Lin-Guanguo/hardware-lab/projects/nfc-business-card/hardware/routing-space-study.md

# 布线空间先行研究

## 当前确定方案

更新于 **2026-09-21**。在重新生成 FreeCAD 外壳或修改 EDA 主工程前，先验证一项平面分区：屏幕固定在左上，长条电池放左下，NFC 保留在右上，USB、充电、电源、屏幕升压和主控尝试集中到右下。这个文件只记录空间假设，不冻结电池型号，也不替换 E9。

研究输入为 84 × 52 mm 外形、现有屏幕/FPC/NFC 参考框和 E9 的功能块。脚本会生成候选电池的二维包络与右下自由区，输出到被忽略的 `artifacts/studies/routing-space/`；它不打开 FreeCAD，不修改 `.FCStd`，也不修改 EasyEDA 工程。

## 先得到的结论

- 屏幕下边约在 `y = 18.5 mm`，假设板内边距为 1.5 mm 后，右下布线区的可用高度约 **16.5 mm**。这是当前分区的主要高度约束。
- 301030 / 301230 横放在左下、从 `x = 2 mm` 开始时，右下连续自由区约 **48.5 × 16.5 mm**；301423 和 301525 较短，右下宽度约 **54.5 / 53.5 mm**。
- 该自由区大于本轮先采用的 **22 × 15 mm USB/电源规划包络**，也大于包含主控和按键的 **40 × 16.5 mm 初步包络**。这些包络是早期筛选值，不是 DRC 或板厂保证。
- 电池放左下会与当前左下的 U1/BLE 天线保留区重叠；因此下一轮必须把 U1 作为右下功能块的一部分重新摆放，并先检查模块天线朝向和边缘净空。
- 这个分区不会侵入当前屏幕、FPC 路径或右上 NFC 参考框，机制上比“电池占掉 NFC 区”更稳妥。

因此，问题已经从“整块板没有通道”缩小为两个可验证问题：

1. 右下 16.5 mm 高的长条能否同时容纳 USB-C 局部扇出、U5/U6、充电器、电源外围和主控；
2. U1 移到右下后，BLE 天线净空是否仍可沿板边保留。

如果这两个问题通过，才值得继续生成新的 CAD 外壳；如果 U1 天线无法在右下安置，应退回 301423/301525 这类较短电池，或保留 U1 左下并重新计算右下最小宽度。

## 候选电池的平面比较

截图中的尺寸和容量是卖家标称。型号中的几何数字可作为初筛，不能代替带保护板、胶带、焊点和引线的最大包络。尤其是 301030，不同供应商目录可出现 60–70 mAh，不能仅凭型号接受 100 mAh；301230 的公开商品示例为 3 × 12 × 30 mm、110 mAh、带 PCM，但也不能证明淘宝同店同批次一致。

| 型号 | 本研究使用的标称包络 | 右下自由区（电池从 x=2 mm 开始，留 2 mm 间隙） | 初步判断 |
| --- | --- | ---: | --- |
| 301030 | 30 × 10 × 3 mm | 48.5 × 16.5 mm | 最窄；容量和完整包体需重点核对 |
| 301230 | 30 × 12 × 3 mm | 48.5 × 16.5 mm | 容量/宽度较平衡，优先询样 |
| 301423 | 24 × 14 × 3 mm | 54.5 × 16.5 mm | 更短，右下更宽；电池左下高度占用较多 |
| 301525 | 25 × 15 × 3 mm | 53.5 × 16.5 mm | 宽且标称容量较低，暂不优先 |

## 下一轮的边界

下一轮只在 EDA 副本中做右下功能块布局，不先改 FreeCAD：

- 保留 E9 原文件；新副本只移动 U1、J1、U5/U6、CC/串联电阻、U2/U3 及其去耦、按键和 SWD；
- 屏幕、J2/FPC 路径、NFC 参考框先不动；
- 先用真实封装检查右下 `16.5 mm` 高度和 USB 插座板边开口；
- 只试 USB_DP/DM、CC1/CC2、VBUS 与 U1 入口，不自动铺开普通信号；
- 通过条件是：关键出口有连续通道、没有新增器件/板边碰撞、U1 天线净空有明确边界；
- 只有通过后，才把验证后的坐标同步到新的 FreeCAD 外壳模型。

可重复命令：

```sh
python3 projects/nfc-business-card/scripts/routing-space-study.py \
  --output-dir projects/nfc-business-card/artifacts/studies/routing-space/<new-run>
```

输出中的 `routing-space-study.json` 是数值记录，`routing-space-study.svg` 是平面比较图。输出目录属于临时验证产物，不提交 Git；脚本和本说明保留。
