Lin-Guanguo/hardware-lab/projects/nfc-business-card/hardware/pcb-e10-button-right.md

# E10 按键右移对照

E10 从 E9 独立复制，将 SW1/SW2/SW3 从 `44.5 mm` 整体移到 `50.0 mm`，板框、USB-C 和其他器件不变。保存重开后几何检查通过，仍为 56 个元件、242 个焊盘、0 段铜线、0 个过孔，DRC 224 条。

右移没有减少 USB/CC 的现有瓶颈；三个按键网络连接到左侧 U1，最短出线距离增加约 5.5 mm。因此 E10 只作为比较工程保留，当前采用 E9 的按键位置。若后续 USB 数据或 VBUS 的明确走线结果显示右侧需要连续通道，再把按键位置与外壳开孔一起复评。
