Lin-Guanguo/hardware-lab/projects/image-oracle/docs/prototype-milestone.md

# 拼接原型阶段收尾与后续路线

日期：2026-09-19。用户确认第三个程序“都正常，效果符合预期”，本阶段定义为：**相机、屏幕与按键的桌面拼接原型完成**。

## 已完成的工作

| 内容 | 当前结果与入口 |
| --- | --- |
| 到货和板卡核对 | 已整理[器件清单](../../../docs/inventory.md)，区分清单、照片与实测结论 |
| 连接、备份与恢复 | USB-UART、原生 USB、下载模式与正常启动流程已记录；保留完整 16 MiB 原厂备份，见[相机启动记录](camera-bringup.md) |
| 程序一：单帧拍照 | [camera_serial](../firmware/camera_serial/README.md)，OV3660 320×240 JPEG 经 USB 保存到 Mac |
| 程序二：显示与按钮 | [display_serial](../firmware/display_serial/README.md)，ST7789 显示、MID 计数；修复快速连按漏计数和 USB 日志阻塞 |
| 程序三：整合原型 | [oracle_live](../firmware/oracle_live/README.md)，左侧约 20 FPS 预览、MID 定格到右侧、下方显示 TRUE/FALSE；用户确认交互、方向和颜色正常 |
| 算法与实机验证 | 固定像素结果可复现；真实右图导出后重算哈希及答案一致；无 USB 读取端时预览和采样继续运行，见[整合实测](oracle-bringup.md) |
| 接线与知识沉淀 | 四张带主板外形、完整丝印和数字序号的 [HTML 接线图](../wiring-diagrams/README.md)；[响应性经验](responsive-input-display.md)、[USB 知识](usb-uart-notes.md)及[统一画图方法](../../../docs/wiring-diagrams.md) |

当前板上程序是 `oracle_live`，旧程序是可单独构建、烧录的实验基线。三个工程固定 Arduino CLI 1.5.1 与 ESP32 core 3.3.11；屏幕相关依赖版本和实际命令保存在对应工程 README。普通断电重插会启动当前已烧录程序，不会自动切换工程。

## 当前边界

- 结构仍是开发板、现成模块、面包板共地和杜邦线连接，桌面体积大、线材分散；尚无定制 PCB、焊接成品或外壳。
- 五向按键目前只接 COM 与 MID，其他方向、SET、RST 未接入；其余传感器、音频等模块未通电验收。
- 答案是冻结缩略图的确定性哈希映射；照片仅在 RAM，断电丢失。尚未扩展答案库或持久保存。
- 已有短时间实机回归和用户体验验收；长时间连续运行、专项长按测试、更高分辨率及整机功耗测量未完成。
- 本阶段完成的是交互功能原型；尺寸、固定方式、连接可靠性和成品装配将进入下一阶段处理。

## 路线一：拼接更多传感器，继续实验

目标是利用现有器件探索更多输入和互动。候选来自已购清单：SHT30 温湿度、GY-302 光照、触摸模块、旋转编码器，以及五向按键的其余功能；具体型号、工作电压和可用 GPIO 在每次实验前核对。

每次选一个模块，先完成独立读取或事件测试，再决定是否接入屏幕页面；保留当前原型作为回退基线。每个实验记录接线、驱动依赖、实际命令、读数和验证结论，接线图沿用现有格式。不要因为增加传感器，就默认改变“图像是 Oracle 唯一变化输入”的规则；若要混入环境数据，应另行明确算法版本。

完成一个实验的标准是能稳定读取或响应、交互仍及时、有可复现记录。后续再决定哪些功能值得保留到紧凑版本，不预先把全部模块纳入最终装置。

## 路线二：焊接、定制电路板与 3D 打印，做紧凑装置

目标是把已经能工作的交互收进可拿起、可固定、可维护的小装置，减少桌面杜邦线。

推进顺序先作为工作草案记录，具体结构和工艺待启动此路线时验证：

1. **确定保留的功能与布局。** 测量当前开发板、屏幕、摄像头、按键和接口的实际外形、孔位及高度；决定显示方向、镜头位置、按键位置、USB 插拔与复位操作空间。
2. **整理连接与装配方式。** 明确哪些模块可插拔、哪些连接焊接固定；比较短线束、洞洞板／转接板和承载现有模块的 PCB。更换接法前整理原理连接表和引脚占用。
3. **定制 PCB。** 在功能和布局相对稳定后绘制原理图与 PCB，逐项核对电源、接口和模块尺寸，再进行打样、焊接和通电验证。是否进一步用模组或芯片替代现成开发板，留待体积需求明确后决定。
4. **3D 打印外壳。** 先验证安装框架、开孔和固定点，再结合实际板卡／线束调整外壳；记录模型、版本和试装问题。开始有真实设计内容时才创建 `enclosure/`。
5. **整机复测。** 验证装配后取景、显示、按键、USB 编程、稳定供电和持续运行，并确认连接固定与拆装维修是否可行。

两条路线可以交替进行；传感器实验保留扩展空间，紧凑版本在绘板前确认本次要保留的功能。本次只记录方向，没有选定制造服务、材料、预算或最终尺寸，也没有发起采购或制作。

## 可恢复基线与归档

当前第三个程序的烧录文件与对应源码已另存本地：

```text
projects/image-oracle/artifacts/firmware/oracle-live-20260919/
```

目录内含四段烧录二进制、`flash_args`、保持相对路径的主程序与头文件，以及 `SHA256SUMS`。8 个文件复制后比对一致，以下校验通过：

```sh
(
  cd projects/image-oracle/artifacts/firmware/oracle-live-20260919
  shasum -a 256 --check SHA256SUMS
)
```

恢复时使用[第三个程序说明](../firmware/oracle_live/README.md#构建烧录与恢复)中的烧录流程，将工作目录换成该备份目录；先确认目标设备和端口。需要从源码重新构建时，使用仓库中的工程及固定工具链。

Git 提交包含源码、脚本、测试、接线图、器件清单、资料来源和实验记录；原始下载、工具链、构建缓存、照片、串口日志、原厂备份及上述二进制基线保存在本机忽略目录。重新克隆仓库不会带回这些本地文件。

## 收尾检查

- Mac 上重新编译运行 `button_debouncer_test.cpp` 与 `oracle_image_test.cpp`，消抖和图像算法测试通过；命令分别见[显示工程](../firmware/display_serial/README.md#编译)与[Oracle 工程](../firmware/oracle_live/README.md#固定算法)。
- 仓库 shell、Python、JSON 语法和 Markdown 本地链接检查通过；8 份接线图 HTML 的内联脚本经 `node --check` 解析通过。语法检查不代替此前的实际显示验证。
- `git diff --cached --check` 通过，提交清单已核对；固件二进制、照片、日志、下载与构建目录的忽略规则生效。
- 本次收尾只更新文档和归档，不重新烧录；实机结果沿用本阶段已完成的测试与用户验收。
