Lin-Guanguo/hardware-lab/projects/nfc-business-card/archive/README.md

# NFC design history

## 当前确定方案

The [active R1 index](../README.md) is the entry point for current work. This archive preserves superseded material; its old "current" statements and manufacturing gates describe their original dates.

- [pre-r1/hardware](pre-r1/hardware/): E-series design studies and evidence.
- [pre-r1/enclosure](pre-r1/enclosure/): superseded models and renders.
- [pre-r1/scripts](pre-r1/scripts/): historical automation; restore the corresponding Git state to reproduce old workflows, rather than running these against R1.
- [pre-r1/docs](pre-r1/docs/): early and alternate plans.
- [pre-r1/readmes](pre-r1/readmes/): previous indexes and progress notes.
- [Move manifest](pre-r1/move-manifest.json): original and new paths, with hashes before relocation. Historical JSON evidence retains its original embedded paths.
- [Historical native EDA projects](../../../eda/archive/nfc-business-card/): E6–E20 and intermediate database checkpoints.

No historical design files were discarded. Markdown links were rebased where targets could be resolved. Local generated outputs remain in `artifacts/archive/` and are not committed.

[Pre-optimization R1 checkpoint](r1-checkpoint/) preserves the original rectangular coil snapshot, Gerber comparison and mechanical source; complete state is commit `ccf9f92`.
