Lin-Guanguo/hardware-lab/projects/nfc-business-card/archive/pre-r1/readmes/projects/nfc-business-card/scripts/README.md

# 电子名片脚本

## 当前确定方案

**R1 workflow:** [check-r1-copper.py](../../../../../../scripts/check-r1-copper.py) checks complete copper including pours, [check-r1-nfc.py](../../../../../../scripts/check-r1-nfc.py) proves the winding is not bypassed, [check-r1-delivery.py](../../../../../../scripts/check-r1-delivery.py) compares the frozen manufacturing package, and [check-r1-case.py](../../../../../../scripts/check-r1-case.py) reopens CAD and checks debug holes and closed meshes. [Commands and evidence](../../../../../../hardware/pcb-r1-delivery.md). Export the guarded live snapshot with [eda-export-r1-snapshot.js](../../../../../../scripts/eda-export-r1-snapshot.js); render actual copper with [render-r1-copper.py](../../../../../../scripts/render-r1-copper.py).

## E20D placement tools

**Current E20D workflow:** [check-e20d-layout.py](../../../../scripts/check-e20d-layout.py) checks placement, USB translation and rear NFC copper exclusions. [e20-clear-shell.py](../../../../../../enclosure/e20-clear-shell.py) takes `NFC_E20_CONFIG=.../e20d-design.json` to generate the coordinated 5.8 mm enclosure. [check-e20b-body-fit.py](../../../../scripts/check-e20b-body-fit.py) accepts `NFC_BODY_REVIEW_REV=e20d` and `NFC_E20_OUT` for native body checks; [render-e20d-front-rear.py](../../../../scripts/render-e20d-front-rear.py) draws native placement plus the explicitly illustrative coil reservation. [Commands, evidence and remaining gates](../../../../hardware/pcb-e20d-front-rear.md).

## Historical E14–E19 workflow

**J1 间隙检查已纠正：**`check-e16-board-fit.py` 现在将统一参考平面的高度差单独标为 `height_below_reference_ceiling_mm`，并用完整 J1 与壳体的 `distToShape` 报告真实距离。E19 对 V7 的名义值为上壳约 **0.34 mm**、下壳约 **0.40 mm**；下文旧的 0.13 mm 仅为参考平面高度差。

更新于 **2026-09-23**。E16 板（三键、L 形板框、右边缘 USB 缺口）的电气连通已核：PCB 原生 DRC 连接 0、只剩 24 项 `Board Outline to SMD Pad`（同一处 0.2007 mm 焊盘到板边的两种分类）、逐引脚网表 56 位号 / 234 引脚 / 0 差异。**增强后的制造包检查发现 Gerber 板框多路径和冲突机械层，E16/E18/E19 当前导出均不通过，不能下单。**外壳 V7 对真实元件模型为名义 0 干涉，尺寸公差仍需核验。当前 CAD 入口是 [e16-enclosure-right-mid-usb-v7.py](../../../../enclosure/e16-enclosure-right-mid-usb-v7.py)，配套校验脚本 [check-e16-board-fit.py](../../../../scripts/check-e16-board-fit.py) 与 [check-e16-usb-plug.py](../../../../scripts/check-e16-usb-plug.py)。E14 空间研究（[e14-layout-study.py](../../../../enclosure/e14-layout-study.py)、[e14-enclosure-v1.py](../../../../enclosure/e14-enclosure-v1.py)）与 V1–V6 外壳样件保留作历史入口。

新的 PCB 开工入口是 [E15 清理版 PCB 开工记录](../../../../hardware/pcb-e15-clean-layout.md)。E15 图页位于 E14 `.eprj2` 工程内；其审查快照由 [generate-e15-clean-layout-svg.py](../../../../scripts/generate-e15-clean-layout-svg.py) 从保存后的 E15 数据生成。该脚本只渲染审查图，不修改 EasyEDA 工程。

右侧中部 USB 方向由 [E16 布局方案](../../../../hardware/pcb-e16-usb-right-mid.md) 推进：[plan-e16-right-mid.py](../../../../scripts/plan-e16-right-mid.py) 用 E15 快照的真实焊盘坐标比较"原布局 / 新方案"的焊盘、模块外形、NFC 保留区和天线净空，输出 [e16-right-mid-plan.json](../../../../hardware/e16-right-mid-plan.json)；[generate-e16-right-mid-svg.py](../../../../scripts/generate-e16-right-mid-svg.py) 直接读取 [e16-right-mid-snapshot.json](../../../../hardware/e16-right-mid-snapshot.json) 画当前审查图——L 形板框、双面铜箔、焊盘与过孔实形、56 个位号、板面自带的层 13 说明文字、禁布区与显示包络，外加右侧的方案面板。禁布区矩形用的是文档记录的边界，因为层 12 的多边形不经桥接导出；其余几何都取自快照。快照用 [eda-export-e16-snapshot.js](../../../../scripts/eda-export-e16-snapshot.js) 从 E16 图页重新导出，否则图会停在旧状态：

```sh
node projects/nfc-business-card/scripts/eda-exec-wait.mjs \
  projects/nfc-business-card/scripts/eda-export-e16-snapshot.js 60000 > /tmp/snap.json
python3 -c "import json,pathlib;d=json.load(open('/tmp/snap.json'))['result'];p=pathlib.Path('projects/nfc-business-card/hardware/e16-right-mid-snapshot.json');p.write_text(json.dumps(d,indent=1,ensure_ascii=False)+chr(10))"
python3 projects/nfc-business-card/scripts/generate-e16-right-mid-svg.py
```

铜箔连通性单独核查：[check-e16-copper-connectivity.py](../../../../scripts/check-e16-copper-connectivity.py) 按真实铜箔宽度判断"两块铜是否搭上"，检查每个网络的焊盘/过孔是否在同一铜簇、以及有没有悬空铜端。**E16 的原生 DRC 即使断网也报"连接 0"，所以动铜箔后必须跑这个脚本**（当前：48 个网络全部连通、死铜端 0）：

```sh
python3 projects/nfc-business-card/scripts/check-e16-copper-connectivity.py
```

原理图与 PCB 的一致性用逐引脚比对核实：[eda-export-pcb-pins.js](../../../../../../scripts/eda-export-pcb-pins.js) 导出 PCB 焊盘网络，[check-netlist-consistency.py](../../../../../../scripts/check-netlist-consistency.py) 与原理图导出的 netlist 做双向差集（当前 56 位号 / 234 引脚 / 0 处差异）：

```sh
node projects/nfc-business-card/scripts/eda-exec-wait.mjs \
  projects/nfc-business-card/scripts/eda-export-pcb-pins.js 60000 > /tmp/pcb-pins.json
# 原理图那份 netlist 已随仓库保存（与验证过的那份 sha256 一致），无需再从客户端导出
python3 projects/nfc-business-card/scripts/check-netlist-consistency.py \
  --sch projects/nfc-business-card/hardware/records/e16-sch-netlist.enet \
  --pcb /tmp/pcb-pins.json
```

**动铜箔之前先离线校验**：原生 DRC 只有铜箔落盘后才能看到结果，而 E16 的"连接 0"并不能证明连通。[plan-nfc-coil.py](../../../../scripts/plan-nfc-coil.py) 按记录好的几何生成 E16 线圈方案（6 圈矩形螺旋 + 两端馈线 + 顶层跨接 + 2 个过孔），[check-proposed-route.py](../../../../../../scripts/check-proposed-route.py) 拿这份方案与实时快照逐点比：线-线 0.102、焊盘/过孔-线 0.152、铜到板边 0.300、孔到孔 0.300，外加"线路自身间距"和禁布区规则（两份禁布区只禁填充/铺铜，允许走线）：

```sh
python3 projects/nfc-business-card/scripts/plan-nfc-coil.py --write     # -> hardware/e16-nfc-coil-plan.json
python3 projects/nfc-business-card/scripts/check-proposed-route.py \
  --route projects/nfc-business-card/hardware/e16-nfc-coil-plan.json
# 期望：ok=true，且 within_route 最差约 0.150 mm（环间距）、其余间隙都在 2 mm 以上
```

方案文件里同时写着落盘前的两个前提：把保留区规则从 `[2,6,5,7]` 放宽为 `[2,6,7]`（去掉禁止走线），以及选择线圈的网表表示（合并两个 NFC 网络，或加一个天线器件+定制封装）。

外壳叠层剖视图由 [generate-e16-v5-section-svg.py](../../../../scripts/generate-e16-v5-section-svg.py) 从几何报告生成（三张切片 + 图例，数字随报告更新）；[generate-e16-height-budget-svg.py](../../../../scripts/generate-e16-height-budget-svg.py) 画的是 5 mm 叠层高度账（电池区剖面 + 各层厚度标注，输出 `enclosure/nfc-card-e16-height-budget.svg`）：

```sh
python3 projects/nfc-business-card/scripts/generate-e16-v5-section-svg.py
```

外壳样件的着色等轴测图与正视顶视图由 [render-stl-iso.py](../../../../../../scripts/render-stl-iso.py) 直接从 STL 生成（不需要 FreeCAD GUI），输出到被忽略的 `enclosure/renders/`：

```sh
python3 projects/nfc-business-card/scripts/render-stl-iso.py
```

NFC 线圈估算：`estimate-nfc-coil.py` 按改良 Wheeler 公式给出螺旋电感、直流电阻、13.56 MHz 谐振电容与 Q，用来判断某块面积能不能做到 1–2 µH：

```sh
# 外圈尺寸按实测可用区填（E16 现在是 10.4 x 21.3 mm，不是早先估的 17 x 21）
python3 projects/nfc-business-card/scripts/estimate-nfc-coil.py --outer 10.7,21.5 --turns 4 5 6 7 8 --width 0.25
```

E16 最初按经验留 5 mm 金属净空，得出 **x 60.60–71.00、y 27.60–48.90** 的六圈候选；这不是硬性射频限制。后续 E18/E19 对比发现其面积使用偏保守，E19 已在独立图页放大为五圈、20.2 × 21.3 mm；实物射频仍待测，详见[面积复核](../../../../hardware/nfc-coil-area-process-review.md)。

空铜区查询：`report-free-space.py` 把快照按 0.1 mm 网格栅格化，给指定区域/层打印占用图并列出最大空矩形（带设计规则余量）。放电池引线走廊、NFC 落点、临时测试点之前先用它量一遍，别凭眼看：

```sh
python3 projects/nfc-business-card/scripts/report-free-space.py --region 33,0,46,19 --layer 1 --limit 3
python3 projects/nfc-business-card/scripts/report-free-space.py --region 54,2,72,26 --layer 2 --limit 3
```

制造包核对：`eda-export-e16-manufacture.js` 一次导出 Gerber/BOM/CPL/装配 PDF（文件落在 `~/Downloads/.cn.lceda.pro.*` 随机名），[collect-e16-manufacture.py](../../../../scripts/collect-e16-manufacture.py) 按内容识别这四个文件并拷成 `artifacts/manufacture/` 下的规范名，`check-e16-manufacture.py` 再把结果与当前快照逐点比对（**唯一闭合板框路径、无冲突机械层轮廓**、板框顶点、钻孔孔数、位号集合、贴装坐标偏差）并写 `manifest.json`。**当前 E16/E18/E19 的重导包均返回 `ok=false`，须修复板框源图或导出配置后重导。**

```sh
node projects/nfc-business-card/scripts/eda-exec-wait.mjs projects/nfc-business-card/scripts/eda-export-e16-manufacture.js 120000
python3 projects/nfc-business-card/scripts/collect-e16-manufacture.py    # 从 ~/Downloads 归纳到 artifacts/manufacture/
python3 projects/nfc-business-card/scripts/check-e16-manufacture.py
```

E19 板框清理仅用于审查：`prepare-outline-review-package.py --source projects/nfc-business-card/artifacts/coil-api-study/expanded-manufacture --output projects/nfc-business-card/artifacts/coil-api-study/outline-cleaned-review`。脚本只接受已复核的 Gerber 结构，删去 J1 辅助线和旧机械参考矩形；输出须再以 E19 快照运行上述检查器。**EDA 源图和正式导出流程仍待修复，审查包不是下单放行文件。**

打印件（STL）的网格体检：[check-e16-print-meshes.py](../../../../scripts/check-e16-print-meshes.py) 直接打开三个 V7 STL，报告是否封闭实体、自相交、非流形边、退化面/重复点，并核对 84 × 52 外框与 4.5 mm 顶面。几何报告查的是 FreeCAD 实体，切片软件只看 STL，所以两个检查都要跑：

```sh
/Applications/FreeCAD.app/Contents/Resources/bin/freecadcmd \
  projects/nfc-business-card/scripts/check-e16-print-meshes.py
```

外壳与**真实元件模型**的干涉检查（不只简化参考盒）：先用 [eda-export-e16-3d.js](../../../../scripts/eda-export-e16-3d.js) 从 E16 图页导出带元件模型的 STEP，等 `~/Downloads/.cn.lceda.pro.*` 的字节数稳定后复制到 `/tmp/e16-board.step`，再用 [check-e16-board-fit.py](../../../../scripts/check-e16-board-fit.py) 在 FreeCAD 里把板抬到 z=0.7 与 V7 上下壳求交：

```sh
node projects/nfc-business-card/scripts/eda-exec-wait.mjs projects/nfc-business-card/scripts/eda-export-e16-3d.js 120000
cp ~/Downloads/.cn.lceda.pro.XXXXXX /tmp/e16-board.step
/Applications/FreeCAD.app/Contents/Resources/bin/freecadcmd projects/nfc-business-card/scripts/check-e16-board-fit.py
```

脚本会过滤导出文件里堆在原点、没有放置的库模型，输出壳体干涉、三条加强筋带（z 3.6–4.0）干涉、三个键帽与实物元件的干涉，以及最高元件到上盖内表面的余量；有真实干涉时退出码为 1。默认读 V7 模型，可用 `--enclosure=...` 换版本。当前结果：918 个导出实体、474 个在板上，壳体/加强筋/三个键帽 **0 干涉**，最高件 J1 余量 0.13 mm。

[pcb-maze-router.py](../../../../../../scripts/pcb-maze-router.py) 是补线阶段用的离线两层迷宫布线器。输入一份几何快照（`pcb_PrimitiveLine` / `pcb_PrimitiveVia` / `pcb_PrimitivePad` 的坐标，单位 mil）和任务表（`[网络, 起点, [目标...]]`，单位 mm），按实际设计规则做障碍扩张后用矢量桶队列 Dijkstra 求路径，输出线段与过孔清单；`--rip` 可先剔除挡路的既有线段，`--pen` 控制拥塞代价让多条线并行挤同一走廊，`--width` 调整线宽。它只写 JSON，改工程由单独的 EasyEDA 脚本完成：

```sh
python3 projects/nfc-business-card/scripts/pcb-maze-router.py --dump snapshot.json --tasks tasks.json --rip rip.json --width 0.15 --pen 40 --out routes.json
```

注意过孔必须 ≥ 7.9 mil 内径 / 11.9 mil 外径，否则既报物理错误又不会被连通性判定接受；DRC 面板是异步的，触发后等待再读，保存重开才得到真实数字。

E14 实际平面图由 [generate-e14-eda-layout-svg.py](../../../../scripts/generate-e14-eda-layout-svg.py) 从 [e14-eda-snapshot.json](../../../../hardware/e14-eda-snapshot.json) 生成；快照同时保留 [器件/焊盘坐标](../../../../hardware/e14-eda-components-pins.json)，用于核对 EasyEDA 保存重开后的真实板框、机械图元和元件位置。该脚本不会修改 EDA 工程。

外壳坐标协调样件由 [e14-enclosure-v2-eda-coordinate.py](../../../../enclosure/e14-enclosure-v2-eda-coordinate.py) 生成；复核使用 [check-e14-enclosure-v2.py](../../../../scripts/check-e14-enclosure-v2.py)。V2 将 USB 开口放在 E14 实际 J1 所在的 y=0 边，只用于解决 PCB/外壳坐标关系。

按键为**三颗**：SW1 (38.1, 3.30)、SW3 (38.1, 15.10) 一列 + 三角第三点 SW2 (46.3, 8.80)，外壳 V7 开三个键孔；菜单仍按两键（一级/二级切换）定义，第三颗接在原本空置的 `KEY_NEXT_N` 上，功能待定。

E14 模型可直接复现：`/Applications/FreeCAD.app/Contents/Resources/bin/freecadcmd projects/nfc-business-card/enclosure/e14-layout-study.py`；几何检查使用 `freecad-study.py check`，视觉检查使用一次 GUI 预览。统一输出到新目录或新文件，保留已有模型；不覆盖其他窗口中的手工或未保存修改。

E14 生产化门槛记录见 [pcb-e14-manufacturing-gates.json](../../../../hardware/pcb-e14-manufacturing-gates.json)。它只记录当前快照和放行条件，不生成制造文件，也不会把未确认的电池尺寸或空间包络当成供应商规格。

器件与**板子材料**的干涉检查：[check-e16-board-clearance.py](../../../../scripts/check-e16-board-clearance.py) 把同一份 STEP 里每个实体与按当前板框拉出的 0.8 mm 板体求交，抓"器件插进板子里"这类外壳检查看不到的问题：

```sh
/Applications/FreeCAD.app/Contents/Resources/bin/freecadcmd \
  projects/nfc-business-card/scripts/check-e16-board-clearance.py
```

这个脚本在 2026-09-23 抓出了真问题：J1 模型与板子相交约 11 mm³，全部落在 x 76.70–77.50 这段 0.80 mm 条带里，而封装自带的板边线在 76.704——说明缺口内缘画浅了。改到 76.704 后当前**通过**（`real_intrusions: 0`）：报告里仍会列出四颗壳脚焊盘被封装画成穿板方块的碎片和 4 µm 贴面接触，两类都按 `surface_contact` / 面积体积阈值标成非真实。结论与复验见 [E16 记录的下标基准复核](../../../../hardware/pcb-e16-usb-right-mid.md#j1-与板框基准复核2026-09-23已修正并复验)。

插头侧复核：[check-e16-usb-plug.py](../../../../scripts/check-e16-usb-plug.py) 按 GCT mating view 的 8.34 × 2.56 mm 插头截面，在 V7 报告量到的 J1 包络上对中插到底，检查插头与注塑头是否撞壳：

```sh
/Applications/FreeCAD.app/Contents/Resources/bin/freecadcmd \
  projects/nfc-business-card/scripts/check-e16-usb-plug.py
```

当前结果：金属壳对上/下壳 **0 / 0 mm³**；能插到接插面的最大注塑头宽度 **9.20 mm**（缺口 9.24 mm），更宽的注塑头会停在卡边、少插 0.8 mm（接插面在卡边内侧 0.8 mm）。

门槛检查：

```sh
python3 projects/nfc-business-card/scripts/check-e14-gates.py
```

EDA 最新为 [84 × 52 E6 功能块工程](../../../../hardware/pcb-e6-84x52-blocks.md)。新增 [check-e6-netlist.py](../../../../scripts/check-e6-netlist.py)，检查 56 元件、234 项原理图引脚与 234 项 PCB 元件焊盘网络；不验证铜线连通、DRC、功耗或 RF：

```sh
python3 projects/nfc-business-card/scripts/check-e6-netlist.py projects/nfc-business-card/hardware/e6-blocks-circuit.enet --pcb projects/nfc-business-card/hardware/pcb-e6-84x52-blocks.json --pcb-netlist projects/nfc-business-card/hardware/e6-blocks-pcb.enet
```

## 常用命令

从仓库根目录运行；环境为本机 FreeCAD 1.1.3 arm64，默认运行时位于 `/Applications/FreeCAD.app/Contents/Resources`。

```sh
/Applications/FreeCAD.app/Contents/Resources/bin/freecadcmd projects/nfc-business-card/enclosure/e14-layout-study.py
/Applications/FreeCAD.app/Contents/Resources/bin/freecadcmd projects/nfc-business-card/enclosure/e14-enclosure-v1.py
/Applications/FreeCAD.app/Contents/Resources/bin/freecadcmd projects/nfc-business-card/enclosure/e14-enclosure-v2-eda-coordinate.py
python3 projects/nfc-business-card/scripts/freecad-study.py check projects/nfc-business-card/enclosure/pcba-e14-battery-layout.FCStd
python3 projects/nfc-business-card/scripts/freecad-study.py preview projects/nfc-business-card/enclosure/pcba-e14-battery-layout.FCStd
printf '%s\n' 'exec(open("projects/nfc-business-card/scripts/check-e14-enclosure-v2.py").read())' | /Applications/FreeCAD.app/Contents/Resources/bin/freecadcmd --console

python3 projects/nfc-business-card/scripts/freecad-study.py generate --variant e6-84x52-detail
python3 projects/nfc-business-card/scripts/freecad-study.py check projects/nfc-business-card/enclosure/pcba-e6-84x52-detail.FCStd
# Optional: one temporary GUI process, then exit.
python3 projects/nfc-business-card/scripts/freecad-study.py preview projects/nfc-business-card/enclosure/pcba-e6-84x52-detail.FCStd
```

生成命令复现宏中的参数，不会导入已保存模型里的手工修改。[freecad-worker.py](../../../../../../scripts/freecad-worker.py) 是内部工作脚本，不直接用系统 Python 启动。完整环境、输出与限制见[软件说明](../../../../../../docs/software.md#84--52-实际封装细化)。

## 其他检查与历史变体

### 布线空间先行研究

在修改 CAD 或 EasyEDA 之前，可先运行 [routing-space-study.py](../../../../scripts/routing-space-study.py) 比较长条电池和右下布线区。它只生成忽略的 JSON/SVG，不覆盖模型或工程：

```sh
python3 projects/nfc-business-card/scripts/routing-space-study.py \
  --output-dir projects/nfc-business-card/artifacts/studies/routing-space/<new-run>
```

研究结论与限制见[布线空间先行研究](../../../../hardware/routing-space-study.md)。

[check-schematic-netlist.py](../../../../../../scripts/check-schematic-netlist.py)核对原 27 元件草案的关键网络，不验证新增 J2/U4/U5、PCB 布线或可制造性：

```sh
python3 projects/nfc-business-card/scripts/check-schematic-netlist.py projects/nfc-business-card/hardware/schematic-draft.enet
```

`baseline`、`e6-302030`、`e6-bottom-usb`、`e6-84x52` 和 `e6-83x51` 保留用于复现旧比较；日常继续当前方案时选择 `e6-84x52-detail`。

### EDA 元件关联复核

`check-e6-netlist.py` 可追加 `--pcb-netlist <PCB 导出的 .enet>`，核对两侧元件集合、Unique ID、封装和引脚网络。与 `--pcb` 的焊盘网络快照检查互补；需从同一工程的正确原理图/PCB 上下文重新导出，不混用旧会话文件。本轮先检出 27 个关联 ID 差异，修正并保存重开后通过。当前功能块副本的复验输入为 `hardware/e6-blocks-circuit.enet`、`hardware/e6-blocks-pcb.enet` 和 `hardware/pcb-e6-84x52-blocks.json`；原 E6 网表与快照保留作历史比较。
