Lin-Guanguo/hardware-lab/projects/nfc-business-card/archive/pre-r1/docs/design-start.md

# 首版设计启动

日期：2026-09-19。

本文件记录首轮空间研究。2026-09-20 已改为优先评估薄模块与定制 PCB/PCBA，并验证 EasyEDA Pro 官方 AI 接口；最新路线见 [PCBA 调研](../../../docs/pcba-ai-workflow.md)。下述现成板模型保留作为早期尺寸对照，尚未替换为定制板布局。

## 本轮决定

- 用户希望先调研、设计并核对方案，尽量减少返工；已授权准备建模软件，认可优先用 Homebrew 管理桌面工具。
- 首先使用 FreeCAD 做器件包络与空间排布。现成小板和定制 PCBA 的选择，在功能兼容性与厚度核对后确定。
- 用户提出首批可能做 **3 个**。目前先作为电路板数量的预算候选，尚未确定下单数量，也未采购。可以先配一套屏幕、电池和外壳调试，其余板备用，整机套数另定。
- 备用板能应对个别焊接、操作损坏，也方便对照调试；同一设计的共同错误仍需要修改。首批制作前应完成下面的资料与验证工作。
- 此前对话中的宽泛总价不作为项目报价。后续以实际 BOM、Gerber 和外壳模型，分别询 PCB、元件、焊接、外壳与运费；改版预留单列。

## 第一份模型要回答什么

目标外形为 86 × 54 × 5 mm，包含键帽等突出部分。第一份 [FreeCAD 空间研究模型](../enclosure/layout-study.FCStd) 表达候选器件的简化包络，生成源为 [layout-study.FCMacro](../enclosure/layout-study.FCMacro)。它不是可打印外壳、PCB 模型或已确认装得下的方案。

| 对象 | 目前采用的依据 | 尚未包含或未验证 |
| --- | --- | --- |
| 外形和壳壁 | 用户外形目标；两面各 0.8 mm 是设计试算值 | 壁厚公差、边框强度、表面处理、固定结构和屏幕窗口 |
| nice!nano 候选板 | 商家截图标称 34.1 × 18 × 3.2 mm | 板卡版本、NFC 引出、最高元件、焊点、USB 插头空间和恢复方法 |
| GDEY0154D67 玻璃 | 原厂图纸 31.8 × 37.32 × 1.0 mm，模型采用尺寸公差上界 | FPC 展开及折弯包络、连接器、驱动板、支撑与安装间隙 |
| 薄电池 | GM201030-PCB 目录标称 30 × 10 × 2 mm | 成品保护包最大尺寸、出线、绝缘、满充尺寸及允许充电电流 |
| 三个按键 | SKQGABE010 主体标称 5.2 × 5.2 × 1.5 mm | 焊盘、支撑 PCB、焊料、键帽及行程 |
| NFC 区域 | 沿用概念图中 23 × 25 mm 的空间分配值 | 真实天线、调谐、电池/屏幕金属层及手持影响 |

器件位置、壳壁和预留区域是本轮设计假设；组件尺寸证据详见 [器件选项](../../../hardware/component-options.md)。模型不绘制未知的驱动板、FPC 和天线几何，避免用猜测填补关键尺寸。NFC 区域只是体积预留，不是可生产天线。

当前主控区的标称厚度试算：`5 - 0.8 - 0.8 - 3.2 = 0.2 mm`。这 0.2 mm 需要同时容纳绝缘、焊点/引线突出、固定和装配公差，因此尚不能判定可装配。

另已下载 [Seeed 官方资源区](https://wiki.seeedstudio.com/XIAO_BLE/#resources) 提供的 XIAO STEP 压缩包，来源与校验值在 [下载清单](../../../docs/download_manifest.json)。该链接归于 Sense 版本，暂作为对照资料；没有用它替换当前候选板，普通版、Sense 和 Plus 的完整包络需要分别核对。

## 设计推进顺序与交付物

1. **核对功能与接口。** 获取具体主控板的原理图、引脚图、USB 下载/恢复方式，核实 NFC1/NFC2 可用。对照一个官方有 NFC 例程的板卡，选定功能验证入口。
2. **补齐完整机械包络。** 选定屏幕驱动/转接板、USB 结构、按钮方案和电池完整保护包，记录最大尺寸、证据和不确定项。更新模型并比较布局，避免只比较产品标称长宽。
3. **先证明最小功能。** USB 供电，验证重新烧录、按键切换两个 HTTPS URI、手机读取新链接；再加入墨水屏验证内容一致。功能样机与尺寸研究可以交替进行。
4. **推进定制板设计。** 按最新路线使用已验证基础接口的 EasyEDA Pro，先画原理图并检查接口与供电，再做布局布线；现成板保留作功能验证。模型、PCB 与 BOM 应引用同一批料号。
5. **制造前复核。** 检查完整厚度、FPC/USB 插拔、按键行程、天线工作环境、烧录救援入口及厂商制造限制；外壳先试装样片，PCB 检查 ERC/DRC。将仿真/检查结果与实物测试分开记录。
6. **按实际文件询价。** 可分别比较 2 块和 3 块 PCBA 的整批报价，以及一套屏幕、电池与外壳。价格确认后再决定首批数量，不因“多一块便宜”提前制造未确认的设计。

## 当前最优先补齐的资料

- 商家那块 3.2 mm 小板的准确商品/版本和原理图，尤其是 NFC 引出与默认充电参数。
- 与所选墨水屏匹配的成品驱动板：完整长宽高、FPC 插入方向和可用软件例程。
- 薄电池的完整包体图及充电规格，不能用电芯型号数字替代。

收到这些资料后，AI 可以继续更新参数模型、输出布局对比及厚度表；用户主要提供实物测量、手感与手机 NFC 读取反馈。软件模型不能代替天线、电源和打印件的实物验证。
