Lin-Guanguo/hardware-lab/projects/nfc-business-card/archive/pre-r1/hardware/board-design-review.md

# 整板评审与下一版实施顺序

## 当前确定方案

2026-09-21：保留 [E6-Blocks 原始工程](../../../../../eda/archive/nfc-business-card/NFC-Business-Card-84x52-E6-Blocks.eprj2)作为试布线基线，暂停逐网补线。USB 工艺边界已完成复核，新的无铜布局副本见 [E7 布局评审](pcb-e7-placement.md)。84 × 52 mm 含壳、薄度优先、屏幕与电池平铺、至少两键的要求不变。**E7 只验证器件通道，不是完成布线。**

E7 已把主控、USB 保护/CC、充电器和 3.3 V 区重新分组，并移除旧试验铜线；下一步只恢复 USB 数据、CC、VBUS 和地回流，关键路径通过后再处理屏幕升压与普通信号。E6 的 638 段线、102 个过孔和 58 条 DRC 继续作为历史对照，不再作为新布局的进度指标。

评审输入为已保存的 [整板画布](pcb-e6-84x52-blocks.png)、[检查快照](pcb-e6-84x52-blocks.json)、[原理图网表](e6-blocks-circuit.enet)及原厂资料。没有重新运行客户端 DRC；58 条是上一轮保存重开后的记录。当前数据不能证明两层不可布，也不能证明改成四层即可完成。

USB 已进一步[复核工艺版本](usb4500-clearance-review.md)：国内 2026-08-15 更新文档明确允许内槽/锣边到铜 ≥0.20 mm；J1 的 24 个距离检查均达到这一名义最小值。保留原封装，取消裁焊盘/缩槽的优先方向。EDA 规则写入未成功，配置已确认未变；E6 的 58 条原生告警仍在，其中 24 条须按新依据更新规则。**这一尺寸问题不再阻塞整体重排，当前转向 E7 的 USB 完整出线及供电路径。** 下文保留早先按 0.30 mm 评审的记录，相关制造判断以本段为准。

USB 整网试布线随后未通过验收，已完整撤回；详见下面的试验记录。**没有新增可保留的布线进展**，不继续在当前固定布局中重复自动布线。

## USB 整网试验与撤回（2026-09-21）

本次假设是：移除 USB 自身的旧铜线，可以解除旧连接对整网出线的限制。保存并在线备份后，仅删除七个 USB 网络中的 30 段线、2 个过孔，调用一次原生自动布线；元件位置、板框与规则不变。API 在 30 秒超时，但读取画布确认已有走线生成，因此没有重复提交布线请求。

重建地铜后，连接告警从 34 变为 31：CC1/CC2 消失，但 GND 从 7 增到 11，VBUS、D+/D− 仍不完整。因为新增地铜分离且 USB 主干未完成，该结果未被接受。尝试仅保留 CC1/CC2、恢复其他 USB 原线后出现间距冲突，因此 CC 也撤回。

最终保存并关闭/重开 PCB，恢复 638 段线、102 个过孔、56 个元件与 58 条 DRC。忽略图元 ID/显示排序后，所有线和过孔的网络、坐标、尺寸及其他属性与试验前一致；元件、独立焊盘、板框、禁布区域及规则内容也一致。恢复部分铜线时重新创建了图元，数据库字节及部分图元 ID 不等同于旧备份，但设计几何与网络属性未改变。

本次只否定“固定当前布局、删除 USB 旧线后由原生自动布线收尾”的方法，不证明两层板不可布。下一阶段必须重新安排主控方向和 USB/充电区，并明确关键线路与回流通道；不能继续以换一组自动布线参数代替布局设计。

原始快照、失败结果和恢复记录位于被忽略的 `artifacts/archive/eda-block-layout/usb-block-*`，修改前数据库备份为 `artifacts/archive/usb-block/baseline.eprj2`。本轮未新增寻路算法，未提交 Git、下单或发消息给工厂。

## 找到的问题与处理决定

| 问题 | 证据与影响 | 处理决定 |
| --- | --- | --- |
| USB 槽边距存在制造冲突 | 基线记录约 0.20 mm，当前规则 0.30 mm；嘉立创公开要求 CNC 板边及内槽到铜至少 0.30 mm。24 条告警含两组检查，不能理解成 24 个独立缺陷 | 优先叠合 GCT 推荐焊盘、开槽、壳体与公差，判断能否在保留装配余量下修正。不能直接降低规则或缩焊盘；若无余量，比较同厚度约束内的替代接口或整理局部工艺确认图 |
| 密脚出口被外围器件和既有铜线占用 | J1 中心 (32, 5.48) mm，U5 (32, 9.5)，U2 (28.1, 13)，U6 (36.1, 10)。数据、CC、VBUS 的出口在同一局部区域竞争；此前局部寻路失败 | 先为全部有效接触脚安排向外出线及错位过孔，再摆 U5/U6、CC 电阻和充电器；不能只验证 A6/A7 到 U5 两条线 |
| 原有铜线变成了不必要的布局约束 | 保留旧铜反复修补；仍有 GND、VBUS、3.3 V 和屏幕供电连接问题 | 新版允许清掉受影响功能块及主干的旧走线，一次布完整网络。保存原版用于对照，不以保留旧走线数量为目标 |
| 主控天线朝向增加 USB 路径约束 | 当前画布的模块天线端朝板内右侧；USB 在其右方，模块 USB 串阻却位于左下。禁布区限制直接连接 | 比较天线端朝外边缘的模块方向，并让 USB 引脚与主干通道相配；必须同时检查屏幕引线和 NFC 馈线，尚未确定新坐标。不能从现有画布直接断言 RF 不合格 |
| 电路与机械仍会改变布局 | VBUS 保护、NTC/充电配置、屏幕峰值及有效电容未定；NFC 尚无线圈与匹配；CAD 落后于实际器件 | 先给这些真实电路留下位置和连接路径，再补普通信号；样品验证前不冻结生产版 |

USB 出线的几何依据：GCT 已存档推荐图中，部分相邻信号焊盘中心距 0.50 mm、宽 0.30 mm，净空仅 0.20 mm。此前局部规划采用 8 mil 线宽、约 6 mil 两侧间距，需要约 0.508 mm。因此该组合不能穿过这类相邻焊盘间隙；应从焊盘端部引出后再展开。此计算只判断该局部通道，不证明整个接口不可布。新增 0.610 mm 外径过孔也不能按 0.50 mm 间距直接并排，应错位布置。

主控型号以网表 `Manufacturer Part = MDBT50Q-P1MV2`、`Supplier Part = C5119772` 为当前选型；库封装/3D 名含 `MDBT50Q-1MV2`。**库名称不同不等于焊盘错误**，但模块方向和高度复核必须按 P1MV2 的原厂图，不能仅根据库名推断天线类型。Raytac 资料要求天线对应区域各层保留净空，并建议靠板边布置。

## 两层与四层的取舍

本轮决定：**先保留两层基线，不立即迁移四层，也不继续按旧布局尝试逐网绕线。** 第一项工作是 USB 封装/出口，不受层数选择影响。

| 方案 | 能解决的部分 | 仍然需要解决 |
| --- | --- | --- |
| 重排后的两层 | 减少功能块交叉；按已确认工艺局部选择线宽、过孔；检验完整 USB 通道及回流 | 底层同时走线和铺地，需要检查地被切断的位置；不能靠任意长绕线完成 |
| 0.8 mm 总厚度的四层候选 | 可安排专用参考地层、独立供电与低速布线空间；增加铜层不必然增加所选成品总厚度 | 须确认国内下单可选叠层、铜厚、公差和 SMT 条件；USB 出口、槽边距和所有层的天线净空仍不能绕过；本轮未取得可下单叠层或报价 |

如果完成一次整块重排后，USB 主干仍必须穿过地平面断口或与电源通道反复冲突，再决定四层。届时按实际叠层设置差分线参数，不把此前 8 mil 普通线宽当作阻抗设计结果。不会以 DRC 剩余数量作为改层依据。

## 有完成标准的工作顺序

1. **USB 制造边界。** 输出一份局部尺寸对照，覆盖焊盘、开槽、壳体、公差及厂商最小间距。结果应为“兼容的修正封装”“满足机械预算的替代料号”或“具体需工厂确认的尺寸”，而不是继续保留模糊告警。需要外部确认时先准备图和问题，不自行发消息。
2. **电路闭合与整块重排。** 补齐 VBUS 保护及电池温度检测设计；明确充电器复位/启动配置。主控方向、USB 保护与充电区一起安排，屏幕升压按开关回路检查，NFC 包括馈线和匹配位置。先出布局和通道，再落全部铜线；大改新建 EDA 文件。
3. **一次验证关键路径。** USB 两组数据接点、CC1/2、VBUS 全部出线；连接到主控的完整数据路径和参考地可检查；电源去耦和开关回路完整。两层不满足时在这里作层数决策，避免继续修补。
4. **普通信号、规则与交付。** 关键路径通过后补按键/I²C/SPI 等，按相关改动复验网表、DRC、保存重开与几何。样品测试及实际 CAD 同步完成后，才讨论制造文件和下单。

每个接口问题最多进行一次有明确假设的修正及一次验证；同类失败再出现就记录证据并讨论，不开发新的临时寻路器。评审文档集中维护在本文件，其他 README 只链接当前入口。

## 本轮验证与资料

- 重新运行 `python3 projects/nfc-business-card/scripts/check-e6-netlist.py projects/nfc-business-card/hardware/e6-blocks-circuit.enet --pcb projects/nfc-business-card/hardware/pcb-e6-84x52-blocks.json --pcb-netlist projects/nfc-business-card/hardware/e6-blocks-pcb.enet`：234 项原理图引脚、234 项 PCB 焊盘网络、112 项关联检查通过。这不验证电路功能或布线质量。
- 查看已保存整板图与 USB4500 推荐图；无新几何检查、RF 仿真、实物测试或客户端 DRC。
- [嘉立创制造工艺要求](https://www.jlc.com/portal/1/serviceGuide)：2026-09-21 查阅，CNC 板边/内槽到铜 0.30 mm；公开过孔要求双层 0.30/0.50 mm、四层 0.20/0.45 mm（孔/外径）。正式订单仍需核对所选工艺。
- [GCT USB4500 产品入口](https://gct.co/connector/usb4500)：沉板接口，主体高 3.16 mm、偏移 0.80 mm；本轮同时查看项目已存档 A1 推荐图，标注推荐 PCB 厚 0.80 mm。网页下载按钮未直接返回新 PDF，不声称已复核最新修订图。
- [Raytac 原厂资料入口](https://www.raytac.com/tw/download/index.php?index_id=24)：使用项目已下载 Version L，第 2.3 节天线布局原则；文件来源及校验值见[下载记录](../../../docs/download_manifest.json)。
