Lin-Guanguo/hardware-lab/projects/nfc-business-card/archive/pre-r1/hardware/pcb-e15-clean-layout.md

# E15 清理版 PCB 开工记录

## 当前确定方案

更新于 **2026-09-22**。下一轮从 E14 工程内的 **E15 Clean Layout - New Battery** 图页开工。E15 是新电池方向的干净 PCB 起点：屏幕左上、长条电池左下、NFC 保留区右上、USB/充电/主控和主要走线区放在右侧；USB 右侧中部作为首选研究方向，底边中部保留为回退。目标外形仍是 **84 × 52 mm**，整机厚度目标 **≤5 mm**。

- 工程：[NFC-Business-Card-84x52-E14-Battery-Layout.eprj2](../../../../../eda/archive/nfc-business-card/NFC-Business-Card-84x52-E14-Battery-Layout.eprj2)
- 图页快照：[e15-clean-layout.json](e15-clean-layout.json)
- 审查图：[pcba-e15-clean-layout.svg](../enclosure/pcba-e15-clean-layout.svg)
- 生成脚本：[generate-e15-clean-layout-svg.py](../scripts/generate-e15-clean-layout-svg.py)
- 旧布局证据：[E14 新电池尺寸主布局评审](pcb-e14-battery-layout.md)

E15 起始快照从 E14 的历史 PCB 图元中清理出 56 个电路元件和 242 个焊盘，起始状态为 0 铜线、0 过孔。当前已完成第一段 `USB_CC2` 可回退走线（4 条线、2 个通孔），工程数据库 `PRAGMA quick_check` 通过，图页坐标快照和 SVG 格式检查通过。E15 仍是布局起点，不是制造稿。

## 首轮现场核对

2026-09-22 已在 EasyEDA 中打开 E14 工程并激活 `E15 Clean Layout - New Battery`。工程树同时显示 `Board1`、`Board1_1`、`Schematic1`、`E6 84x52 - 电路整合与试布线`、E15 和 `Panel1`；E15 当前以 PCB 图页打开，文档类型为 PCB，图页 UUID 为 `4991220fd7f692a5`。

- 关联前工程源显示 E15 的 `board` 关联为空，`Board1` 仍关联旧的 E6 PCB。本轮已保留 `Board1/E6` 作为回退，并新建 `Board1_1`，将 E15 与同一份 `Schematic1` 绑定。
- E15 当前快照仍为 56 个元件、242 个焊盘、0 条铜线、0 个过孔、1 个区域和 10 条板框/机械折线；板框几何按 84 × 52 mm 保存，但“PCB 裸板尺寸”与“含外壳边缘尺寸”尚未在客户端确认。
- 快照中的 Layer 11 板框带有底边缺口：约从 `x=43` 到 `56 mm`、深约 `6.5 mm`；J1 为 `USB-SMD_USB4500-03-0-A`，中心约在 `x=49.53 mm, y=5.46 mm`。这只能作为当前几何基线，下一步要按实物连接器外形和外壳开口重新核对。
- 快照中的 DRC 基线为 8 个普通间距错误、12 个同封装间距错误和 200 个连接错误，共 220 项。它们只用于开工前对照，不代表已完成的在线 DRC 结果。
- 本轮先通过本地 Bridge 完成只读核对，再通过 `dmt_Board.createBoard(Schematic1, E15)` 写入关联；写入后已读取确认 E15 的 `parentBoardName=Board1_1`，未改动 `Board1/E6`。

## USB 机械基线

`J1` 当前封装为 `USB-SMD_USB4500-03-0-A`。 [GCT USB4500 产品资料](https://gct.co/connector/usb4500) 将该系列标为 USB 2.0 Type-C、水平侧插、中置安装；页面给出的连接器本体长度为 6.50 mm，产品高度为 3.16 mm，偏移高度为 0.80 mm。它们是供应商宣传/目录参数，尚未替代手上实物的卡尺测量和外壳试装。

- E15 当前底边缺口深度约 6.5 mm，与目录中的连接器本体长度处于同一数量级，可作为暂定机械入口基线。
- E15 当前缺口宽度约 13 mm。公开资料中的推荐 PCB 开口尺寸仍需结合具体版本图纸核对，暂不据此直接改板框。
- 项目已有 [USB4500 槽边距复核](usb4500-clearance-review.md)：原封装焊盘到槽后边约 0.20 mm，按当前公开工艺下限可继续保留，但这不是订单级确认，也不替代 E15 的外壳试装。
- 因此，当前 8 项普通板边间距错误和 12 项 J1 同封装间距错误先按“待机械确认”分类；不为了清零 DRC 而盲目缩小缺口、移动 J1 或删除封装外形。需要优先核对的是板边到外壳窗口、锚脚和插拔包络。
- 在拿到实际连接器或确认外壳开口后，再决定 Layer 11 是按连接器本体开口、插头插拔包络还是外壳窗口留量重画。

## 在线 API 核对

重启 EasyEDA 后，API Gateway 已在本地 `49620` 端口连通。在线读取确认：当前文档仍为 E15（`documentType=3`，UUID `4991220fd7f692a5`），E15 已属于 `Board1_1`，其原理图为 `Schematic1`；原 `Board1` 继续保留 E6 关联。

在线 DRC 与快照一致，共 220 项：

- 8 项普通间距错误，其中包含主板框与 R1、J1 通孔的边缘冲突。
- 12 项同封装间距错误，全部集中在 J1 封装外形与其 USB/电源/地焊盘之间。
- 200 项连接错误，说明 E15 仍是完全未布线的布局起点；USB、充电/电源、按键、屏幕和主控网络都还没有铜线连接。
- 关联后按元件设计ator与焊盘号逐项比对：56 个元件、234 个元件焊盘的网络与保存的 E14 网表快照完全一致；额外 8 个焊盘是 E15 保留的测试点/独立焊盘，不改变原理图元件网表。

因此下一步的实际顺序已经收敛为：先确认 USB4500-03-0-A 的实际外形/开口包络，按机械依据处理 J1 与 Layer 11 的边界冲突；再以已关联的 `Board1_1/Schematic1` 为网表基准，开始 USB 和电源网络布线。在线 API 核对和关联写入均已完成，本轮没有改动旧的 `Board1/E6`。

## 首段 USB 走线

已在 `Board1_1` 中写入并保存 `USB_CC2`：J1 的 `B5` 先接到 `R2_1`，再从 U6 的 CC2 焊盘通过两个通孔转到底层，回到 `R2_1`。6 mil 线宽、12/24 mil 通孔经过在线 DRC 复核，没有新增间距错误，连接错误从 200 项降为 197 项；关闭并重开 E15 后仍保持 4 条线、2 个通孔和 `parentBoardName=Board1_1`。完整坐标、图元 ID 和回退基线见 [E15 USB CC2 首段快照](e15-usb-cc2-route.json)。

`USB_CC1` 暂不照搬同一路径：J1 的 A5、R1 与当前底边缺口相互处在板边冲突区域，直接走线会新增轨迹到焊盘/板边错误。待板框与外壳窗口基准确认后再处理，避免把临时绕线固化为机械错误。

## 右侧中部 USB 评审

已复制 E15 做 [E16 右侧中部 USB 布局方案](pcb-e16-usb-right-mid.md)。用户确认右侧中部更符合卡片形态，方案已给出板框、`J1`、`U1` 和 USB 小元件的具体坐标，并通过焊盘级离线校验（相对本页无新增冲突）。E16 方案尚未写入 EasyEDA：本机 Run API Gateway 扩展未连上桥接服务，重连后落盘并跑原生 DRC；在那之前本页仍是可回退的布线基线。

## 开工顺序

1. **统一基准已完成。** E15 已关联到新建的 `Board1_1/Schematic1`，旧 `Board1/E6` 保留回退；接下来明确 84 × 52 mm 是 PCB 板框还是含外壳边缘的目标尺寸，未确认前不继续画板框和外壳。
2. **锁机械入口。** 根据实际 J1 封装、插拔方向和外壳边界重画右侧中部 USB 开口；同时确认 Layer 11 板框、锚脚、槽边到铜和工艺边。底边中部开口只作为 E15 回退方案保留。
3. **放真实电池边界。** 先使用交付最大包络，而不是只使用 30 × 12 × 3 mm 标称值；包络要包含保护板、胶带、焊点、引线和鼓胀余量。未取得供应商数据前，电池只能作为可替换的保守占位。
4. **验证连接关系。** 从原理图重新导出网表，在 E15 中核对元件关联、封装和关键电源网络；记录未布线数量作为新基线。
5. **按风险布线。** `USB_CC2` 已完成首段；待板边基准确认后处理 CC1，再依次处理 USB DP/DM、VBUS、GND 回流、充电/SYS/BAT、3V3、主控 USB 和屏幕关键时序；每个区块保存、关闭、重开并重新跑 DRC。
6. **再同步 CAD。** 只有板框、J1、屏幕/FPC、电池包络和按键位置冻结后，才从 E15 坐标生成外壳开口、支撑和装配公差。现有 E14 V1/V2 只作验证样件。

## 本轮放行条件

- E15 图页与原理图 Board 关联明确，保存重开后元件和网络一致。
- PCB 板框、USB 缺口、屏幕/FPC 区、电池包络和 NFC 净空使用同一坐标基准。
- 关键 USB/电源网络有可审查的走线，DRC 结果按类别记录；未解决的连接或板边错误不能被标记为完成。
- 实际电池和屏幕到货前，不冻结厚度、壳体卡扣或供应商制造文件。

本阶段不生成 Gerber、Excellon、最终 BOM/CPL、生产 STEP 或可直接打印的外壳。E14、E13、E9 及其他历史工程保留用于回退和比较。
