Lin-Guanguo/hardware-lab/projects/nfc-business-card/archive/pre-r1/hardware/pcb-e17-coil-study.md

---
description: E17 板载 NFC 线圈候选、原理图连网解法、PCB/CAD 验证与射频待办
last_updated: 2026-09-23
status: coil_geometry_verified_rf_matching_pending
---

# E17 板载线圈候选

这是 E16 的**独立研究图页**，保存在 [原始 EDA 工程](../../../../../eda/archive/nfc-business-card/NFC-Business-Card-84x52-E14-Battery-Layout.eprj2) 内的 `Board1_3`；`Board1_2` 仍是未放线圈的 E16 基线。E17 已解决“线圈两端网络不同，铜箔无法落板”的工具问题，并把线圈、换层、制造数据及当前 V7 外壳配合实际验证了一遍。**没有匹配电容，也没有实测谐振或读距；不得据此直接投产。**

## 解法和设计边界

- 嘉立创 EDA 专业版 API 实有 `sch_PrimitiveComponent.createShortCircuitFlag(x,y,rotation,mirror)`。在候选 MCU 原理图页放 `(605,565,90,false)`，短接符两脚落在 `y=555/575` 的 NFC 导线端点；导出网表中 U1 pin 52、54 都是 `NFC1_TBD`。此前按工程底层数据里的负 y 放符号会悬空，不能合网。
- 候选 PCB 的两条原有馈线、两块自由落点焊盘和六圈螺旋都改为 `NFC1_TBD`。这是**直流连通的网表表达**，不等于短接了 13.56 MHz 的线圈：物理铜线从一脚经螺旋到另一脚。短接符只允许 EDA 正确识别这条连续导体，不能替代 RF 仿真或量测。网名 `NFC1_TBD` 仍是占位名。
- 外圈范围 `x=60.60–71.00, y=27.60–48.90 mm`；底层六圈，0.25 mm 线宽、0.15 mm 铜边间隙；顶层一段内端跨接，新增 2 个 12/8 mil 过孔。模型估算 `L≈1.12 µH`、`Q≈139`，**均未实测**。线圈在阻焊下，底层不露铜；需要按实际叠层、屏幕、电池及金属壳测谐振与读距。
- `Board1_3` 由 `Board1_2` 复制，独立的原理图和 PCB 页。EDA 的 `pcb_Document.importChanges()` 虽返回成功却未把 PCB 网名同步到两块落点/馈线，故逐一改名并复核了网表与连通性。复制前后的 E16 基线仍为 56 元件、244 焊盘、791 线、168 过孔。

## 已验证

| 检查 | E17 候选结果 |
| --- | --- |
| 保存后重开 | 56 元件、244 焊盘、820 铜线、170 过孔；短接符与合并网名仍在 |
| 路线净空 | `check-proposed-route.py`：`ok=true`，0 违规，线圈环间最小铜边距 0.15 mm |
| 原生 PCB DRC | 24 项均为 E16 已知 J1 槽边 `Board Outline to SMD Pad`；新增违规 0 |
| 原理图与 PCB | 56 位号 / 234 引脚，0 网名差异；独立铜连通检查 47 网，0 断网、0 悬空端 |
| 制造导出 | Gerber、钻孔、BOM、CPL 从 E17 重导；17 个 Gerber 成员、170 个过孔钻孔命中、56 位号一致，底层阻焊文件无螺旋开窗。**旧数量检查 `ok=true`，二次板框完整性检查改判失败：GKO 多一路径、GME 多一完整矩形**，见 [整板复核](pcb-e19-independent-review.md) |
| CAD | 从 E17 导出 STEP，与现有 V7 外壳检查：0 实质外壳/肋位/键帽干涉；这不验证射频负载、薄壁打印质量或电池尺寸 |

长期核查数据见 [E17 验证记录](records/e17-coil-validation-2026-09-23.json)。工作快照和制造导出保存在被 Git 忽略的 `projects/nfc-business-card/artifacts/coil-api-study/`；可再生的 EDA 源文件以仓库内工程为准。线圈脚本为 [apply-e17-coil-study.js](../scripts/apply-e17-coil-study.js)：它要求候选 PCB 尚处于 791 线/168 过孔的复制初态，只负责最后的落铜，不要在已经落铜的 E17 上重跑。路线净空检查也必须对落铜前快照运行，不能让新增铜线与自身重复比较。

## RF 必须修正的地方

[Nordic nRF52840 NFCT 规格](https://docs.nordicsemi.com/r/bundle/ps_nrf52840/page/nfc.html)明确要求线圈差分接在 NFC1/NFC2 之间，**两侧各有一只外部谐振电容，且总电容应匹配**。E16 记录把 `1.12 µH` 对应的 `123 pF` 差分等效电容，直接换成“100 pF + 15 pF 两个并联位”；那不是已验证的双端器件值。若假设两只完全相同、对地电容且忽略寄生，`C_equiv=C_each/2`，因此每侧的理想起算值约 `246 pF`；实际值必须扣除模块、芯片、焊盘、走线和环境寄生，再经实板测调。这个计算仅用来指出原估算的拓扑错误，**不是可直接采购或贴装的定值**。

下一版需先确定模块 NFC 引脚与板载线圈之间两侧各一处匹配焊位及接地回路，在原理图和 PCB 同步落地，再重跑网表、DRC、连通性、制造包和外壳检查。随后测线圈电感/电阻及装壳后的 13.56 MHz 调谐，用 PN532 与手机测试正反面、方向、读距和 USB/电池金属负载。当前 E17 只证明几何和 EDA 表示可行。
