Lin-Guanguo/hardware-lab/projects/nfc-business-card/archive/pre-r1/hardware/pcb-e6-84x52.md

# 84 × 52 mm 六色屏电路整合与试布线

## 当前确定方案

2026-09-21：新增独立 [NFC-Business-Card-84x52-E6.eprj2](../../../../../eda/archive/nfc-business-card/NFC-Business-Card-84x52-E6.eprj2)，保留此前排布工程。含壳 84 × 52 mm、优先薄度、至少两键的约束不变；电池仍在右下 PCB 缺口，屏幕与电池平铺，右上保留 NFC 空间。

本版将 GDEH0154E01 的 24 针接口、屏幕电源开关、升压/负压外围和 USB 数据线/CC 防静电加入原理图与 PCB。共 56 个元件、234 个元件焊盘，另有 8 个 SWD/电池/NTC 焊盘。**试布线草案，不是制造文件**。完整屏幕刷新、功耗、充电、NFC 和外壳装配均未实测。

- [原理图网表](e6-circuit.enet)、[PCB 网表](e6-pcb.enet)、[检查与 PCB 快照](pcb-e6-84x52.json)、[EDA 画布](pcb-e6-84x52.png)。
- [引脚检查脚本](../scripts/check-e6-netlist.py)核对原 27 元件基线及本次 29 个新增元件；网络相等不代表走线连通或硬件正确。
- 最新 FreeCAD 仍是 [pcba-e6-84x52-detail.FCStd](../enclosure/pcba-e6-84x52-detail.FCStd)。其中旧 J2 和屏幕外围占位块**尚未同步本版实际器件**，不能用此前 36 个简化形体检查替代本版装配验证。

## 本版电路选择

| 位号 | 器件 / LCSC 编号 | 当前用途与边界 |
| --- | --- | --- |
| J2 | FPC-05FB-24PH20 / C2856831 | DESPI-E01 同款 24P、0.5 mm 双面接触座；方向、插入深度、FPC 厚度及公差等样品确认 |
| U4 | TPS22919DCKT / C2860814 | 3.3 V 屏幕电源开关；QOD 接输出。先深睡、处理 GPIO 电平再关电，防止信号脚反灌 |
| U5、U6 | TPD2EUSB30DRTR / C97502 | 分别保护 USB D+/D− 和 CC1/CC2；选非 A 的 5.5 V 型号。VBUS 浪涌保护尚未补齐 |
| L1 | NRH3010T470MN / C223116 | 47 µH、额定/饱和电流约 250 mA 的候选，不是 500 mA；须核对启动峰值、损耗与替代供应 |
| Q1 | Si1308EDL-T1-GE3 / C469327 | 1=G、2=S、3=D；屏内控制器驱动外部升压 |
| D1–D3 | MBR0530T1G / C82046 | 1=阴极、2=阳极；升压和负压电荷泵 |
| R13、R14、R18 | 100 kΩ、10 kΩ、10 kΩ | EN 下拉、GDR 下拉、BUSY 上拉到可关断的 EPD_VDD |
| R15、R16、R17 | 2.2 Ω、0 Ω、3 Ω | RESE 采样、VPH→VGH、BS0 接地；R15 功率需按峰值/占空比复核 |
| C14、C15、C19 | 4.7 µF / 25 V / X7R / 0805，C98195 | 采用 DESPI 参考板配置作为可调整草案，不能声称与屏型号规格书差异已消除 |
| C9–C13、C16–C18、C20–C22 | 1 µF / 50 V / X7R / 0805，C28323 | 输入/输出去耦及高压外围；工作电压下有效容值尚未验证 |

J2 的 1、6、7 脚按 GDEH0154E01 型号规格书不连接；没有照搬通用 DESPI 图的温度传感器接口。2=GDR、3=RESE；8=BS0；9=BUSY；10=RESET；11=DC；12=CS；13=SCK；14=SDI；15=VDD；17=GND；其余电源脚见网表与[接口对照](../../../docs/gdeh0154e01-evaluation.md#接口与参考电路复核2026-09-21)。保留 MCU 原有 `*_TBD` 网络名便于追溯，不表示 FPC 引脚号未知。

官方依据：[Good Display 型号资料入口](https://www.good-display.com/product/983.html)、[TPS22919 规格书](https://www.ti.com/lit/ds/symlink/tps22919.pdf)、[TPD2EUSB30 规格书](https://www.ti.com/lit/ds/symlink/tpd2eusb30.pdf)、[Si1308EDL 规格书](https://www.vishay.com/docs/63399/si1308edl.pdf)。DESPI 原图与型号规格书的本地文件/校验值见[资料清单](../../../docs/download_manifest.json)。

## 排布与检查边界

屏幕座中心 (51.53, 34) mm；外围电容在右侧窄条，升压/开关在屏幕后方 PCB 上；排线转弯区域 x=39.42–48、y=26.2–42.7 mm 避开器件主体。NFC 仍只是 x=60–82、y=24–50 mm 的 22 × 26 mm 保留区，尚未画线圈或确定匹配电容。双面地铜边界限制在 x≤59.5 mm，并保留 BLE 禁布区域。

平面检查分别比较真实库焊盘的旋转包围框、装配主体、板轮廓与 FPC/NFC 保留区；不包含排线曲面、焊锡高度、屏幕后背接触、外壳弹片及实际电池公差。L1 等库中 3D 高度与料号规格也需在同步 CAD 时逐一确认。

## 本次验证结果

- 磁盘重开后：56 个元件、234 个元件焊盘及 8 个独立测试/电池焊盘仍在；检查脚本通过 234 项原理图引脚与 234 项 PCB 元件焊盘网络比较。
- 平面几何：器件之间焊盘包围框相交、主体相交、焊盘越界、NFC 区焊盘侵入和 FPC 弯折区主体侵入均为 0；不是整机 3D 装配验证。
- PCB：648 段铜线、107 个过孔、双面地铜。DRC **67 条**：43 条连接性错误、24 条 USB 槽边距；27 个元件关联 ID 修正并保存重开后，原生网表差异消失。连接性错误按对象统计，不等于 43 条独立网络；详见 JSON 按网络汇总。
- 原理图 DRC：API 返回 7 条警告，未报告错误；尚未通过完整工程评审。
- 视觉与持久化：第 3 页 13 条过期说明经 API 精确选中、原生“编辑 → 删除 → 已选”清除；第 1/2 页另替换 4 条过期说明。全部图页保存重开后旧文案未恢复，第 3 页画布已检查。先前的错误 PDF 不沿用，本轮未重新验收制造 PDF。
- SCH/PCB 关联：27 个元件的位号、封装与引脚网络一致，但 PCB Unique ID 仍为旧值。按位号将 PCB ID 对齐原理图后，112 项 ID/封装及导出引脚网络比较通过；关联修复阶段 56 个元件位置/旋转及铜线、过孔、地铜保持不变；随后本轮仅调整走线与过孔。详见[排查记录](../../../docs/software.md#e6-保存与关联排查2026-09-21)。
- `.eprj2` SQLite `PRAGMA quick_check` 为 `ok`；未提交/移动仍打开的工程数据库。旧版 EDA/CAD 未覆盖。

复验命令（仓库根目录）：

```sh
python3 projects/nfc-business-card/scripts/check-e6-netlist.py projects/nfc-business-card/hardware/e6-circuit.enet --pcb projects/nfc-business-card/hardware/pcb-e6-84x52.json --pcb-netlist projects/nfc-business-card/hardware/e6-pcb.enet
git diff --check
```

保存与关联问题本轮已处理；接下来收敛布线、供电与天线，实物确认后同步结构，尚不能生产。

## 本轮局部布线（2026-09-21）

- 将 J2 旁阻挡出线的 4 段 BUSY 顶层走线改为跨层连接，保留原有 MCU/上拉分支；接通 `EPD_VSNL1`、`EPD_VSNH`、`EPD_VCOM`。合计新增 20 段线、4 个普通通孔，净增 16 段线。
- 新线宽 8 mil，过孔约 0.305 mm 孔径 / 0.610 mm 外径；未放宽规则。重建铺铜、保存重开后 DRC 从 73 降到 67，未新增间距告警，原生网表差异未复发。
- 56 个元件位置、旋转和关联 ID 与修改前一致；屏幕区画布已检查。该视觉检查不证明电源回流、高压轨或装配可用。
- SYS 引脚与屏幕 VDD 的局部寻路，在保留现有铜线及过孔尺寸的条件下未找到通路；不是全局不可布的证明。下一轮需局部重排出线，优先供电、地与 USB 成对走线，避免新增长绕线仅为减少 DRC。
- 本轮原始记录及在线备份保存在被忽略的 `artifacts/archive/eda-routing-close/`；API 过孔刷新现象见[软件说明](../../../docs/software.md#e6-局部布线与过孔检查2026-09-21)。

## 制造前必须解决

1. 完成残余连接，后续修改继续复验原生网表与关联 ID；自动布线结果需要按电源回路、回流、线宽、过孔与 USB 成对走线复评，不能只追求 DRC 数字下降。
2. USB4500 库封装信号焊盘距槽边约 0.20 mm，而当前规则要求 0.30 mm，产生板框和封装内板框两组告警。需结合 GCT 推荐开槽、0.8 mm 板厚、铣槽及装配公差解决；未降低全局规则来隐藏问题。
3. 明确屏幕配置差异：BUSY 极性、参考板与型号规格书的电容取值差异；样品确认 FPC 插合方向和 pin 1，再测刷新时间、峰值电流、电源压降与高压轨。
4. 复核 200 mA LDO、250 mA 电感、升压开关/二极管及电池最大电流是否满足刷新；电池 NTC/充电温度保护和 150 mAh 小电池限流还需定案。
5. 补齐 VBUS 保护，设计 NFC 线圈/匹配并实测；评估屏幕、电池、铜与手持对 RF 的影响。
6. 更新实际器件 CAD，验证 ≤5 mm 厚度、FPC 弯折、USB 槽强度、键帽/薄壳与装配顺序，再生成制造文件。
