Lin-Guanguo/hardware-lab/projects/nfc-business-card/archive/pre-r1/hardware/pcb-e7-placement.md

# E7 布局评审版

## 当前确定方案

2026-09-21：以 [NFC-Business-Card-84x52-E7-Placement.eprj2](../../../../../eda/archive/nfc-business-card/NFC-Business-Card-84x52-E7-Placement.eprj2) 作为新的布局评审副本。它从 E6-Blocks 复制而来，只保留板框、禁布区、器件和网络，不保留试验铜线；原 E6 工程和 638 段线的版本继续保留作对照。E7 不是生产工程，不能直接导出下单文件。

这次的目的，是先验证 USB、充电和主控之间有没有清楚的通道，再决定是否值得重新布线。主控放到左侧 NFC 保留区下方，USB 数据串联电阻放到保留区下沿；USB 保护、CC 电阻和充电器集中到接口下方，屏幕 FPC 与升压区保持原位置。这个布局仍需结合实物模块天线方向、FPC 折弯和外壳高度复核。

屏下/NFC 保留区仍按原方案保留，约为板上部中间的 `15–25 mm × 1.5–15 mm` 矩形；本轮只允许走线沿其下沿或右侧通过，没有把它变成普通布线区。后续如果要把铜线带入这块区域，必须先重新确认线圈尺寸、屏幕背面材料和隔磁方案。

| 功能块 | 中心位置（mm） | 方向 | 说明 |
| --- | ---: | ---: | --- |
| U1 MDBT50Q-P1MV2 | 9.2, 19.0 | 0° | USB 脚从下方出线；NFC 禁布区未移动 |
| J1 USB-C | 32.0, 5.475 | 0° | 机械锚点，沿板边保留 |
| U5 USB 数据 ESD | 32.0, 9.5 | −90° | 靠近 J1 |
| R3/R4 USB 串联电阻 | 17.2, 15.8 / 17.0 | 0° | 位于 NFC 保留区下沿，等待成对出线 |
| U6 CC ESD / R1/R2 | 37.0, 10.0 / 39.0, 8.5 / 11.5 | 0° | 与数据通道分开 |
| U2 充电器 / U3 3.3 V | 35.0, 15.0 / 39.0, 15.0 | 90° / 0° | VBUS、SYS 和 3.3 V 形成一个局部电源块 |
| J2 FPC / U4 升压 | 51.53, 34.0 / 原位置 | −90° / 0° | 本轮不改屏幕区 |

SWD 五个测试焊盘移到左下方一排，避开主控封装；它们仍是救援/首烧接口，位置还要和外壳开口一起定。

## 检查结果

- 从 E6 副本清除 638 段线、102 个过孔和 2 个铺铜后保存，再关闭并重开 E7；重开后仍为 56 个元件、242 个焊盘、0 段线、0 个过孔、0 个铺铜。
- 重开后的器件间距检查没有 SMD Pad-to-SMD Pad、测试焊盘或器件重叠错误。
- 仍有 12 条板边到 USB 焊盘和 12 条同一插座内的旧规则提示；它们属于 J1 沿板边的既有工艺检查，和本轮器件排布无关。
- 连接错误是预期结果：E7 尚未放回任何铜线，所以不能用这些连接错误判断布局失败，也不能用“0 段线”判断已完成布线。

## USB 关键路径试验

本轮用脚本做了两次有边界的手工路径试验，范围只包括 USB_DP/USB_DM、USB_CC1/CC2 和 USB_VBUS；每次都在试验结束后删除铜线、保存并重开，当前 E7 没有留下试验铜线。

- 两次试验都能让 USB 相关网络不再出现在连接错误列表中，说明布局的主通道方向是可行的。
- 但第一次产生 121 条新的安全间距错误，第二次仍产生 90 条，主要集中在 USB-C 双面触点的 A/B 数据焊盘扇出、U5 的 GND 焊盘、U2 充电器焊盘入口和主控两条 USB 逃线交汇处。
- 因此这不是可以直接下单的布线结果。当前 E7 保持干净的 0 线/0 过孔状态；试验脚本和 DRC 原始结果保存在 `artifacts/archive/eda-block-layout/e7-usb-route-attempt.*`、`e7-usb-route-v2.*`，供下一轮针对冲突点修改。

这次试验说明，当前速度瓶颈主要是 USB-C 局部扇出和电源入口，不是屏下/NFC 区域本身。下一轮应先换 USB-C 扇出策略或调整 J1/U5/U6 的局部位置，再继续铺开普通信号。

## USB 位置候选

当前 E7 的 J1 已经位于下方长边（中心约 `32.0, 5.475 mm`）。因此下一轮不把“整只 USB 换到另一条边”作为默认解，而先比较同一条边的局部平移；单独移动 J1 不足以解决问题，需要把 U5、R3/R4、U6、R1/R2 和 U2 当成一个 USB/充电小组一起移动。

| 候选 | 预期收益 | 新增风险 | 判断 |
| --- | --- | --- | --- |
| 下长边向左平移约 5–7 mm | 更接近 R3/R4 和主控数据出口，给右侧充电器/CC 区留出横向通道 | 需要复核 USB 槽、按键和外壳插拔力；不能侵入 U1 天线净空 | **优先做 E8 局部变体** |
| 下长边向右平移 | VBUS 可能更接近 U2 | 数据线更长，容易进入电池/FPC/充电拥挤区 | 暂不优先 |
| 改到左短边 | 理论上可缩短主控数据线 | 靠近 U1 天线和左侧结构，插拔方向及天线净空更难 | 作为备选 |
| 改到右短边或上长边 | 可避开当前下边局部 | 会侵入电池、FPC、屏幕或 NFC 保留区 | 暂不采用 |

实际建立的 [E8 USB 左移评审工程](../../../../../eda/archive/nfc-business-card/NFC-Business-Card-84x52-E8-USB-Left.eprj2) 将 USB/CC 小组左移约 2.5 mm 后重开检查。J1 原本嵌在板框约 9.2 mm 的 USB 开口中，两个固定孔分别卡在缺口两侧；左移后新增板框到通孔、板框到孔各 1 条冲突。因此“同一条边向左平移”不能只改器件位置，已降级为失败候选，详细记录见 [E8 评审](pcb-e8-usb-left.md)。

这些候选只改变布局假设，不能代替 USB-C 封装内部 A6/B6、A7/B7 的扇出验证；扇出是与连接器位置无关的局部瓶颈。

## 下一轮验收

1. 先在当前 E7 中只安排 USB_DP/USB_DM、USB_CC1/CC2 和 USB_VBUS 的出口，检查数据对、CC 支路和地回流是否有独立通道。
2. 关键 USB 路径通过后，再安排 U2/U3 的去耦和屏幕升压回路；普通按键、SPI 和 I²C 最后处理。
3. 如果两层板在这个新布局中仍需要反复穿过禁布区或切断地回流，再拿具体冲突决定是否评估四层；不根据旧的 638 段线或 DRC 总数换层。

本轮未验证 RF、NFC 线圈、阻抗、功耗、FPC 插合、实物高度或外壳装配。主控旋转和 SWD 焊盘移动也需要在正式布局冻结前结合 Raytac 天线图与 FreeCAD 复核。
