Lin-Guanguo/hardware-lab/projects/nfc-business-card/archive/pre-r1/hardware/pcb-e8-usb-left.md

# E8 USB 左移评审

## 当前结论

E8 是从 E7 复制出的独立失败候选，不是生产工程。它把 J1、U5、U6、R1/R2 组成的 USB/CC 小组向左平移约 2.5 mm，用来验证底边是否还有局部调整空间；E7 没有被修改。

验证结果表明，J1 不能在现有板框中直接横移。板框上已有一个约 9.2 mm 宽的 USB 开口，J1 的两个固定孔分别位于开口两侧。左移后，右侧固定孔落到板框边界上，重开后的 DRC 新增 1 条板框到通孔和 1 条板框到孔的冲突；一次中间试验还出现过 R2 与 C1 的焊盘重叠，已在 E8 中消除。E8 最终仍为 56 个元件、242 个焊盘、0 段线、0 个过孔、0 个铺铜，但不能作为可制造方案。

因此，当前 USB-C 最稳妥的位置仍是 E7 的原开口位置。若要把 USB-C 换到左短边、右短边或上长边，必须同步重画板框缺口、修改外壳插口，并重新安排 U5/U6、CC 电阻、充电器入口和地回流；这已经是新的机械/PCB 方案，不是简单拖动一个器件。

## 工程与证据

- [E8 USB 左移工程](../../../../../eda/archive/nfc-business-card/NFC-Business-Card-84x52-E8-USB-Left.eprj2)：独立失败候选，保留用于对照，不能下单。
- [E7 布局评审记录](pcb-e7-placement.md)：当前采用的干净布局副本和 USB 扇出试验记录。
- [E8 左移重开检查](records/e8-final-reopen.json)：记录位置、元件数量、铜线数量和 DRC 结果。

## 下一步

先保持 E7 的 J1 位置不变，集中优化连接器内部 A6/B6、A7/B7 的扇出、U5 的数据出口和 U2 的 VBUS 入口。只有当局部两层布线仍无法形成连续通道，才另建“换边 USB”方案，并把板框和 FreeCAD 外壳一起作为一个变更评审。
