Lin-Guanguo/hardware-lab/projects/nfc-business-card/archive/pre-r1/hardware/pcb-e9-usb-local.md

# E9 USB 局部紧凑排布评审

## 当前确定方案

E9 是从 E7 独立复制出的布局候选，保持 84 × 52 mm 板框、USB-C 开口和两层板假设不变。它只调整 USB/充电局部器件：U5 下移并左移到 `30.5, 12.0 mm`，U6 移到 `35.5, 10.0 mm`，R1/R2 回到 `39.0, 8.5 / 11.5 mm`。按键、屏幕 FPC、电池和外壳边界没有改动。

E9 保存后重开仍为 56 个元件、242 个焊盘、0 段铜线、0 个过孔、0 个铺铜；DRC 为 224 条，和 E7 基线相同，未新增器件重叠或板框冲突。它是比 E7 更紧凑的 USB/CC 排布候选，仍不能生产。

## 关键路径试验

在 E9 上只恢复 CC1/CC2 的受控试线，得到 8 段线和 4 个过孔。两条 CC 网络均连接到 J1、U6、R1/R2，DRC 从 224 条降到 218 条，未新增安全间距或物理错误。试线随后已清除，E9 正式文件保持无铜。

USB 数据双面焊盘的完整扇出仍未通过：局部两组过孔和 U5 数据出口会互相挤压。独立的 [E11 数据扇出对照](pcb-e11-data-fanout.md) 已尝试两轮错开通孔，仍在 CC1、数据线彼此和 U5/C1 入口处产生冲突，且 DP/DM 没有闭合；试验已清除。后续应比较内部过渡封装、另一面 ESD 或可制造的盲/埋孔与四层叠层，不把长距离自动布线当作布局完成。

## 按键移动比较

按键目前位于 `44.5 mm` 纵列，USB/CC 区在其左侧；已验证的 CC 通道不经过按键之间。为验证用户允许的调整空间，另建 [E10 按键右移工程](../../../../../eda/archive/nfc-business-card/NFC-Business-Card-84x52-E10-Button-Right.eprj2)，将 SW1/SW2/SW3 整体移到 `50.0 mm`。

E10 保存重开后仍为 56 个元件、242 个焊盘、0 段线、0 个过孔，DRC 仍为 224 条，未带来 USB/CC 的新通道收益；按键网络到左侧 U1 的距离反而增加约 5.5 mm。由于按键并未阻挡当前 USB 扇出，E10 不替换 E9，仅作为机械/布线对照保留。若后续数据或 VBUS 试线明确需要右侧走线廊道，再重新评估按键位置和外壳开孔。

## 验证记录

- E9 保存重开：[e9-final-reopen.json](records/e9-final-reopen.json)
- E9 CC 受控试线：[e9-usb-cc-only-run.json](records/e9-usb-cc-only-run.json)
- E10 按键右移保存重开：[e10-final-reopen.json](records/e10-final-reopen.json)
- E10 按键网络焊盘位置：[e10-key-pads.json](records/e10-key-pads.json)

以上检查只覆盖 EDA 几何、连接性和保存重开；未验证 USB 阻抗、RF/NFC、FPC 插合、实物高度、电池安全或外壳装配。
