Lin-Guanguo/hardware-lab/projects/nfc-business-card/archive/pre-r1/enclosure/card-holder-option.md

---
description: 用户提出的成品 PP 卡套面板与 3D 打印增高中框方案
last_updated: 2026-09-17
status: candidate_pending_measurement
---

# 成品卡套 + 打印中框

**历史方案：不再作为当前成品优先路线。** 2026-09-20 用户要求含外壳边缘不超过银行卡，本页 97 × 66 mm 候选不符合新约束；仅保留薄面板与打印框的结构思路，见[当前紧凑方案](compact-layout.md)。

此前思路： 成品面板负责薄而平的前后表面，打印件负责边框高度、内部定位和承力。它能避开大面积薄打印面板的难点，也允许先验证是否真的需要增高。

## 截图能确认什么

用户在 2026-09-17 提供商品截图，选项写着“容量：97 × 66 × 3 mm 竖款”，外观有透明/半透明面、周边成型边缘和挂绳孔。用户提出用 PP 前后片，但截图本身没有显示材质证明。

尚不能确认：97 × 66 × 3 是实际可用内腔、可容纳纸卡尺寸还是营销规格；外部轮廓/总厚度；面板各多厚；是否可拆为两片；是硬质 PP、其他塑料还是不可拆的柔性袋。商品链接/型号待补充。没有因图片而直接确认“这款能装下”。

若这里确实是可用内腔，平面面积比 86 × 54 mm 更宽裕，但成品外形还要更大，属于另一个尺寸选项。不能把“内腔可装 3 mm”写成“整个壳厚 3 mm”。

## 按难度排序的三种做法

| 做法 | 怎么做 | 采用条件 |
| --- | --- | --- |
| **R1：直接用原卡套** | 元件固定在薄定位支架/定制 PCB 上，放入原壳；按键和充电触点开孔 | 实测净高足够，原卡扣能完全扣合，整机最高点 ≤5 mm |
| **R2：原前后片 + 增高中框** | 保留两片，打印匹配其边缘的台阶/夹持框，增加所需净高 | 可以无损拆片；原凸边、卡扣和中框的嵌套高度已量测 |
| R3：标准薄片 + 自定中框 | 裁切 PP/PET/PC 前后片，打印中框，避免原卡套凸边 | 原壳外尺寸/扣边太厚或难适配时更直接；薄片仍是采购件 |

优先试 R1；净高不够才做 R2。不要先加一圈中框，再发现原壳已经足够装下。R2 原有卡扣在增高后可能无法工作，中框必须承担新的固定功能，不能默认还能原样扣紧。

## 一个厚度示例

若得到的是两片平面薄板，且元件平铺：

```
前片 0.50 + 前胶层 0.10 + 内腔净高 3.20
          + 后胶层 0.10 + 后片 0.50 = 4.40 mm
```

这里 3.20 mm 是前后片内表面之间的净高；中框在同一高度围住元件，**不再另外叠加一个 3.20 mm**。框的盖边、卡扣或键帽若伸到面板外，要另计最高点。数字是设计示例，不是截图商品的实测规格。

上面的 3.20 mm 净高来自早期 nRF52832 方案：0.90 mm PCB 上界 + 0.10 mm 焊接 + 1.70 mm 模块 = **2.70 mm**。用户新增 USB 编程需求后，当前 nRF52840 模块候选的相同计算为 **3.20 mm**，还没留固定间隙；不能继续将 3.20 mm 净高视为足够。可研究 3.5–3.7 mm 净高与更薄面板，并单独核对 USB-C 最大包络。电池仍不垫在整块 PCB 上面。[更新后的尺寸分析](../../../docs/usb-and-prototyping.md)

保留原壳凸边时，先测原壳总厚 `T0` 与可用净高 `G0`，再决定要增加多少净高。只有边缘嵌套关系不变时，才可近似用 `Tnew = T0 + (Gtarget - G0)`；实际扣边和台阶可能让结果不同。

## 热熔胶与 PP 粘接

热熔胶可以用来做早期局部固定，但不建议让普通胶棒形成的一圈胶同时负责精确增高和主要承力：胶珠高度不均、返修不便，具体胶种也未必能粘牢 PP。

PP 属于低表面能塑料，常规胶粘剂未必可靠；有专门适配的胶带和聚烯烃热熔胶，不能泛化成“任何热熔胶都不行”或“热熔胶都能粘”。原厂依据：[3M 的 PP/LSE 粘接说明](https://www.3m.com/3M/en_US/bonding-and-assembly-us/applications/material-bonding/lse-plastics/)、[Henkel 用于 PP 的聚烯烃热熔胶](https://next.henkel-adhesives.com/uk/en/products/industrial-adhesives/central-pdp.html/technomelt-as-5303/BP000000073809.html)。

推荐做法：

1. **中框定位与夹持为主。** 台阶限制面板移动，框支撑 PCB 和玻璃边缘；需要拆装的阶段用可拆固定方式。
2. 胶只在边缘受控胶槽中辅助固定。若确认是 PP，可以把 3M 300LSE 系列薄胶带作为试样候选，按具体型号厚度计入叠层；“适配 PP”不等于已验证这款卡套的表面涂层与脱模剂。[3M 薄胶带说明](https://www.3m.com/3M/en_US/bonding-and-assembly-us/double-sided-tape/thin-bonding-tape/)
3. 若使用热熔胶，在空壳试片上验证粘接与变形，不往电池软包、屏幕 FPC 或玻璃上直接浇热胶；不用胶块填满电池周围的余量。

## 对按钮、屏幕和 NFC 的影响

- 前片有磨砂纹理时先隔着它看小字和二维码；不清晰就切显示窗口或换透明片。
- 按钮开孔后由中框支撑开关附近 PCB，按压力不传给玻璃或电池。整片 PP 的可弯曲性不能直接当成可靠按钮机构。
- 前后普通未金属化塑料片不会像金属壳那样屏蔽 NFC，但电池金属包、屏幕结构、金属挂绳扣和导电装饰仍需按最终装配测试。挂绳金属扣尽量远离预留 NFC 区。
- 不购买带金属层、RFID 屏蔽层的“防盗刷卡套”作为 NFC 面板。
- USB-C 日常编程/充电口由中框侧面开口访问，并留足插头空间；SWD 留作首烧/救援。不要封胶后才发现无法插入 USB 或进入恢复模式。

## 样品量测表

| 项目 | 当前状态 |
| --- | --- |
| 材质标识 / 产品型号 | 待确认 |
| 是否前后可拆 / 拆开方式 | 待确认 |
| 外部长 × 宽 × 最大厚度，含挂孔与凸边 | 待量测 |
| 内腔可用长 × 宽 × 净高 | 待量测 |
| 前片、后片平面厚度 | 待量测 |
| 周边凸边、扣合深度、加强筋 | 待量测 |
| 屏幕隔片清晰度 / 按键开孔效果 | 待试样 |
| PP 与候选胶带/热熔胶粘接表现 | 待试样 |

先取得这些数据就能决定 R1/R2/R3，不需要先安装完整机械 CAD。该选项已纳入项目，没有代替用户决定最终外观或扩大尺寸。
