Lin-Guanguo/hardware-lab/projects/nfc-business-card/enclosure/nfc-card-e14-enclosure-v1-isometric.png

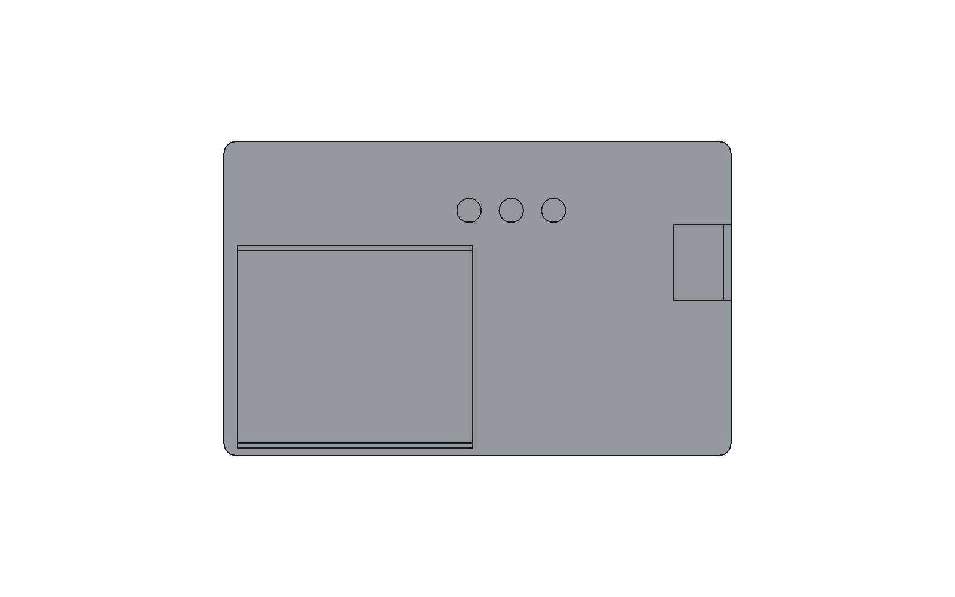
projects/nfc-business-card/enclosure/nfc-card-e14-enclosure-v1-isometric.png
