Lin-Guanguo/hardware-lab/projects/nfc-business-card/enclosure/nfc-card-e16-enclosure-v1-review.png

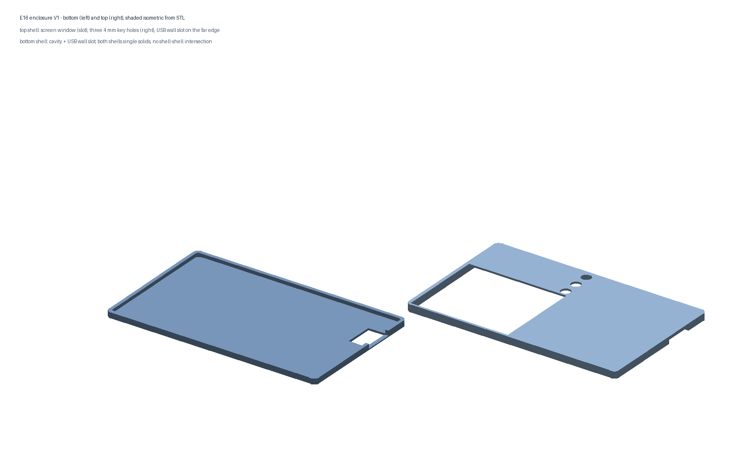
projects/nfc-business-card/enclosure/nfc-card-e16-enclosure-v1-review.png
