Lin-Guanguo/hardware-lab/projects/nfc-business-card/enclosure/pcba-e6-84x52-detail.png

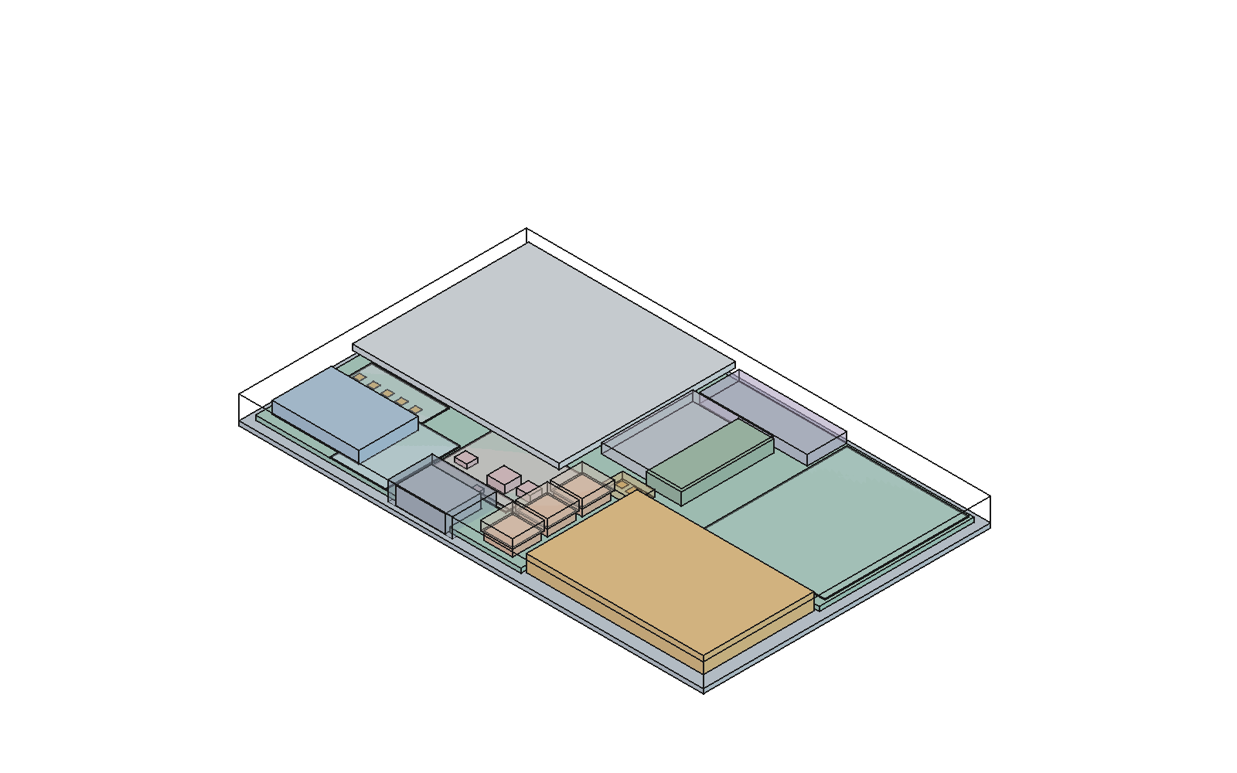
projects/nfc-business-card/enclosure/pcba-e6-84x52-detail.png
