Lin-Guanguo/hardware-lab/projects/nfc-business-card/enclosure/r1-clear-5.8/e20-clear-open-iso.png

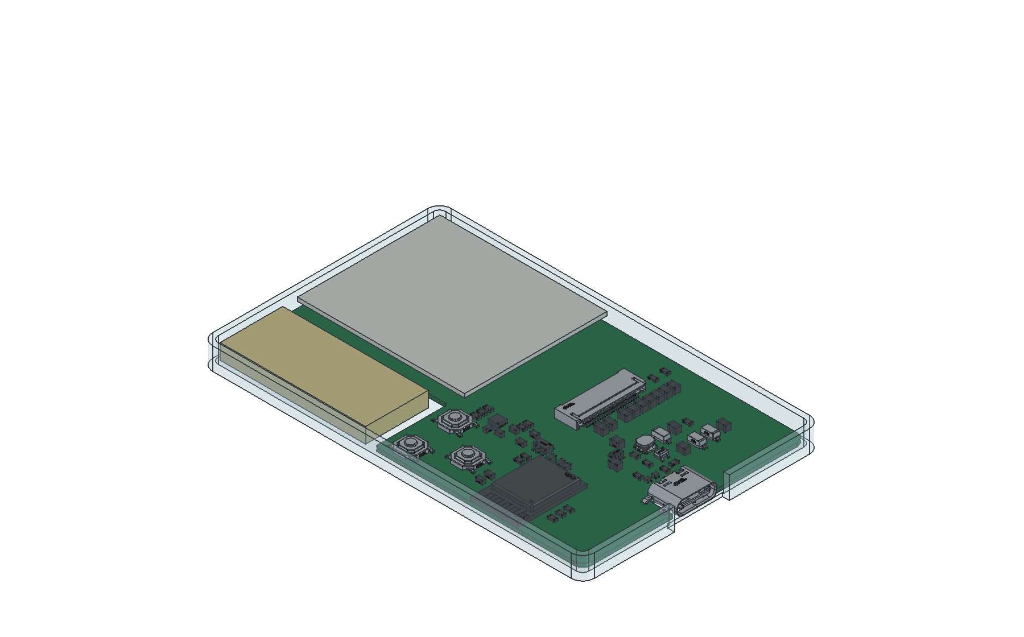
projects/nfc-business-card/enclosure/r1-clear-5.8/e20-clear-open-iso.png
