Lin-Guanguo/hardware-lab/projects/nfc-business-card/enclosure/renders/e16-board-routing.png

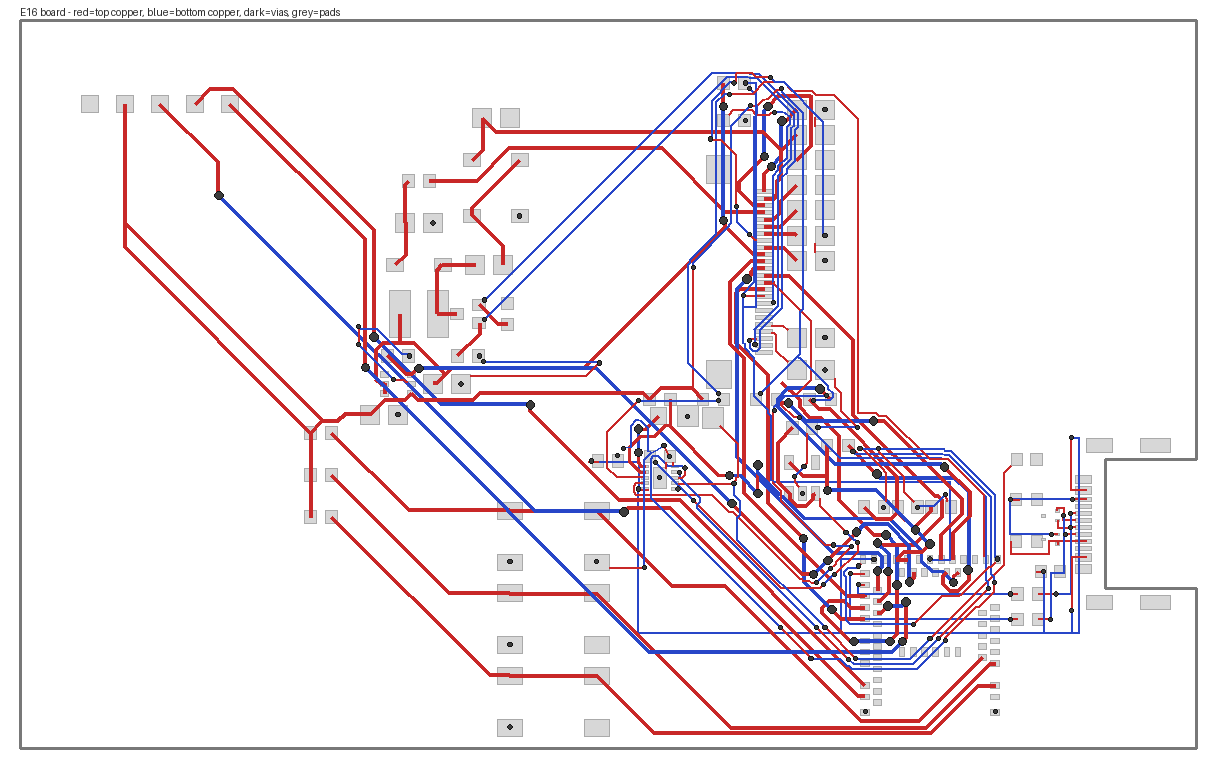
projects/nfc-business-card/enclosure/renders/e16-board-routing.png
