Lin-Guanguo/hardware-lab/projects/nfc-business-card/enclosure/renders/e16-enclosure-v5-iso.png

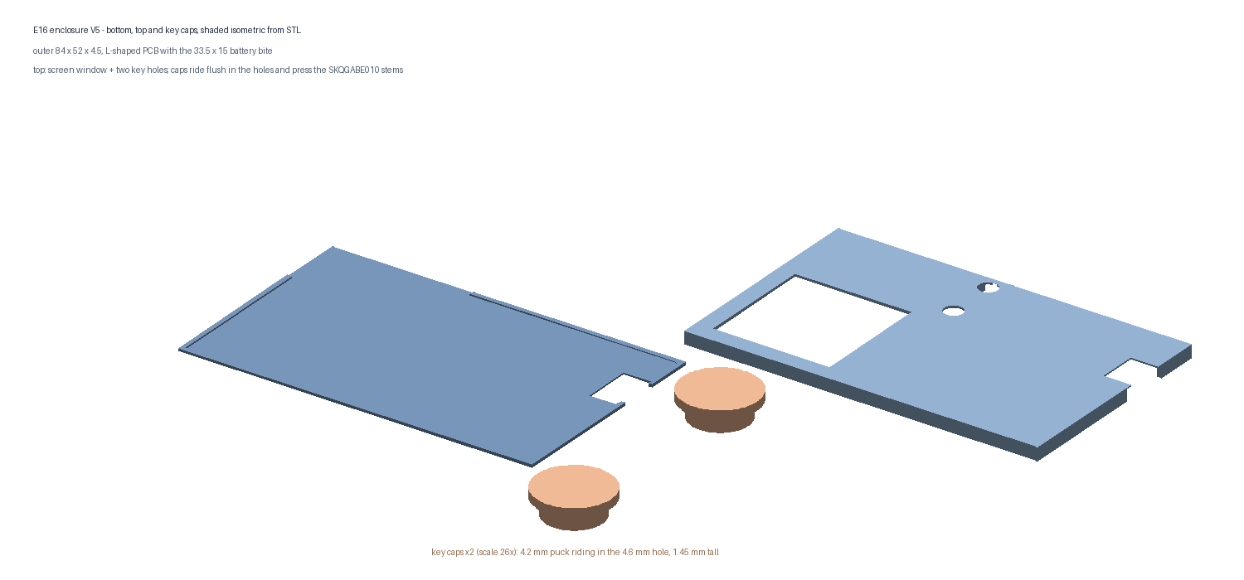
projects/nfc-business-card/enclosure/renders/e16-enclosure-v5-iso.png
