Lin-Guanguo/hardware-lab/projects/nfc-business-card/enclosure/renders/e16-enclosure-v7-top.png

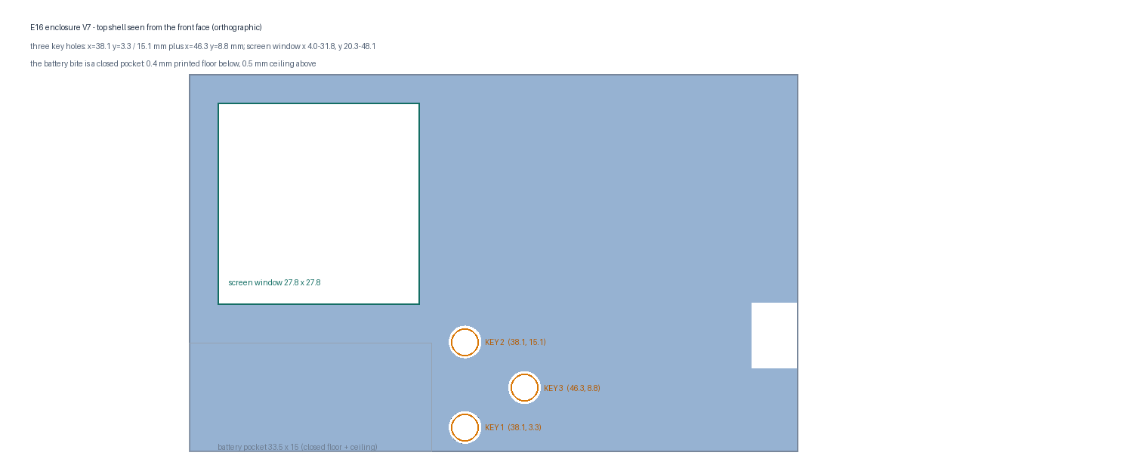
projects/nfc-business-card/enclosure/renders/e16-enclosure-v7-top.png
