Lin-Guanguo/hardware-lab/projects/nfc-business-card/enclosure/renders/r1-control-routing-comparison.png

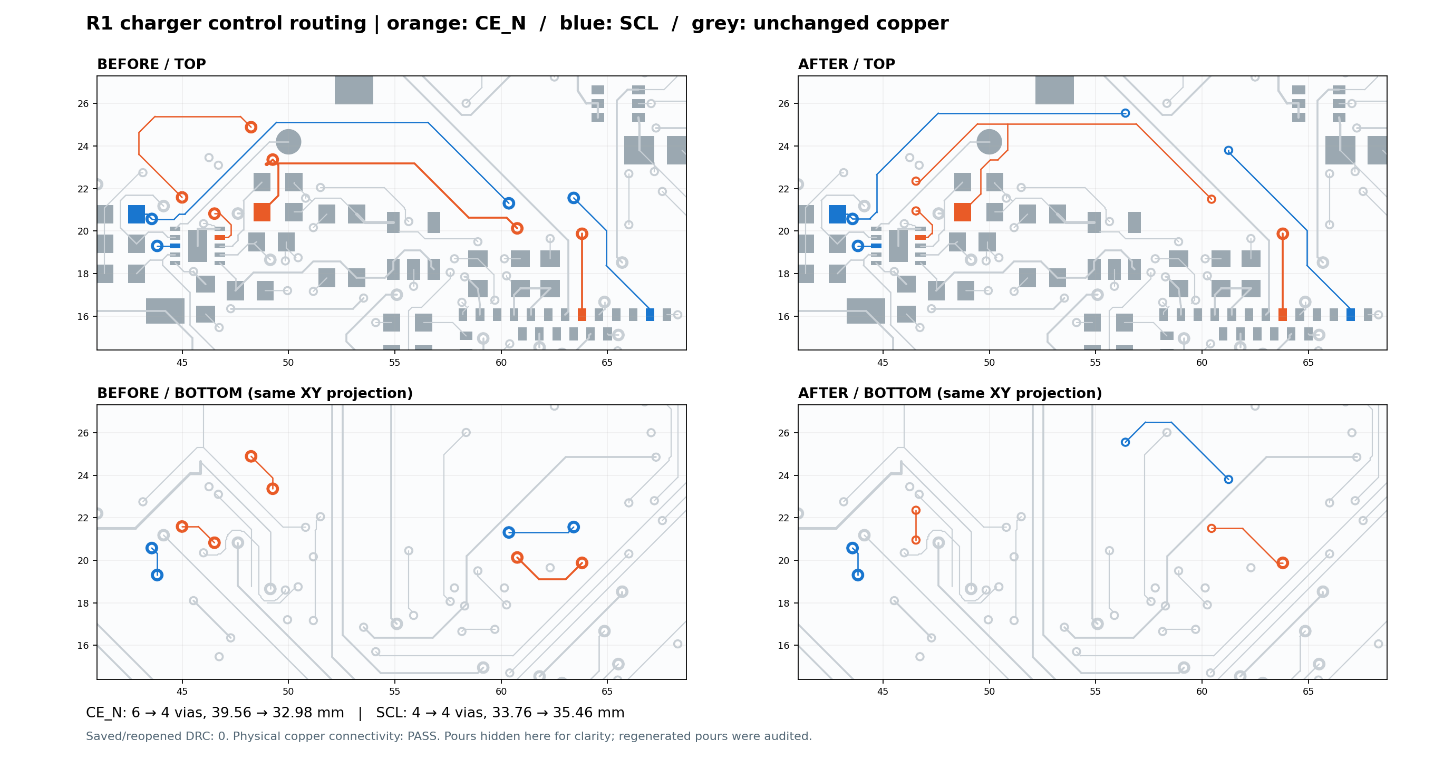
projects/nfc-business-card/enclosure/renders/r1-control-routing-comparison.png
