Lin-Guanguo/hardware-lab/projects/nfc-business-card/hardware/pcb-e6-84x52-blocks.png

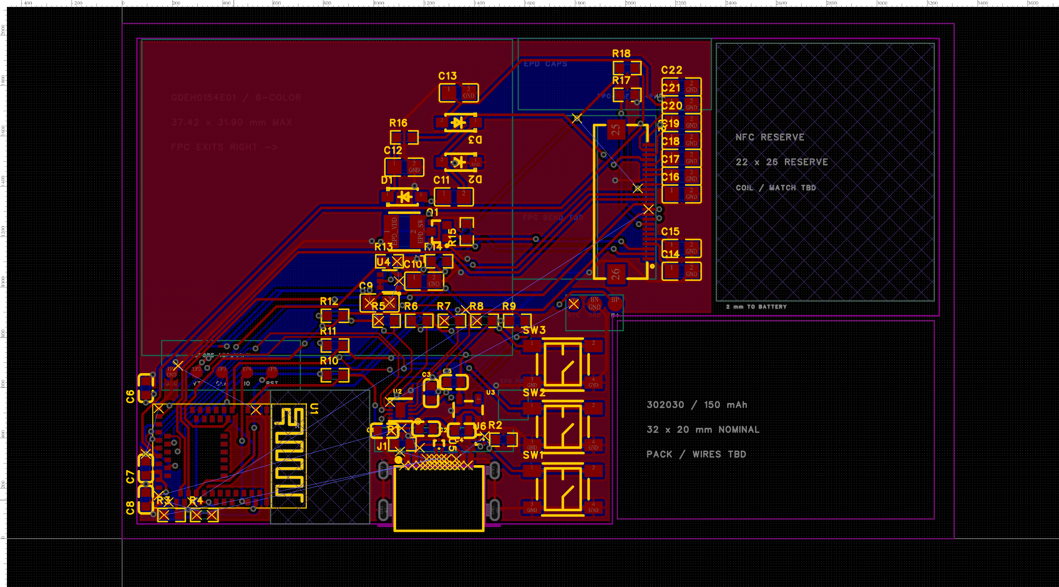
projects/nfc-business-card/hardware/pcb-e6-84x52-blocks.png
