Lin-Guanguo/hardware-lab/projects/nfc-business-card/enclosure/r1-usb-height-5.2/rear-cover-study.FCStd

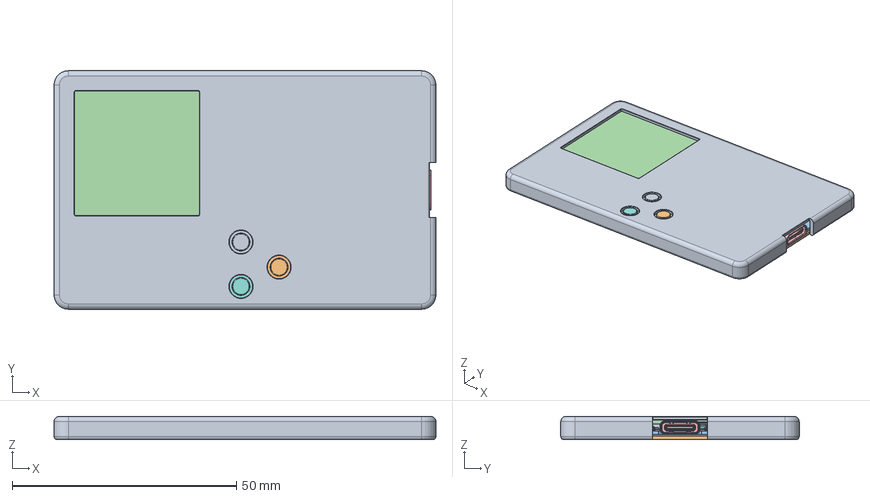
[picture p50: CAD file, 2026-09-24]
projects/nfc-business-card/enclosure/r1-usb-height-5.2/rear-cover-study.FCStd
85.2 x 53.2 x 5.20 mm
RoundedUpperShell
InsetRearCover
PCB
Component_C9
Component_C10
Component_C11
Component_C12
Component_C13
Component_C14
Component_C15
Component_C16
Component_C17
Component_C18
Component_C19
Component_C20
Component_C21
Component_C22
Component_C1
Component_C2
Component_C3
Component_C4
Component_C5
Component_C6
Component_C7
Component_C8
Component_C23
Component_C24
Component_R1
Component_R2
Component_R3
Component_R4
Component_R5
Component_R6
Component_R7
Component_R8
Component_R9
Component_R10
Component_R11
Component_R12
Component_R13
Component_R14
Component_R15
Component_R16
Component_R17
Component_R18
Component_U1
Component_U4
Component_D1
Component_D2
Component_D3
Component_U5
Component_U6
Component_U2
Component_J2
Component_U3
Component_Q1
Component_L1
Component_SW1
Component_SW3
Component_SW2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
