Lin-Guanguo/hardware-lab/projects/nfc-business-card/enclosure/r1-usb-height-5.2/upper.step

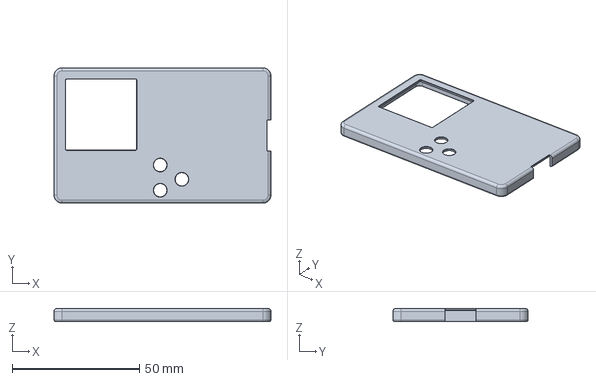
[picture p51: CAD file, 2026-09-24]
projects/nfc-business-card/enclosure/r1-usb-height-5.2/upper.step
85.2 x 53.2 x 5.20 mm
