Lin-Guanguo/hardware-lab/projects/nfc-business-card/enclosure/r1-usb-height-5.4/upper.step

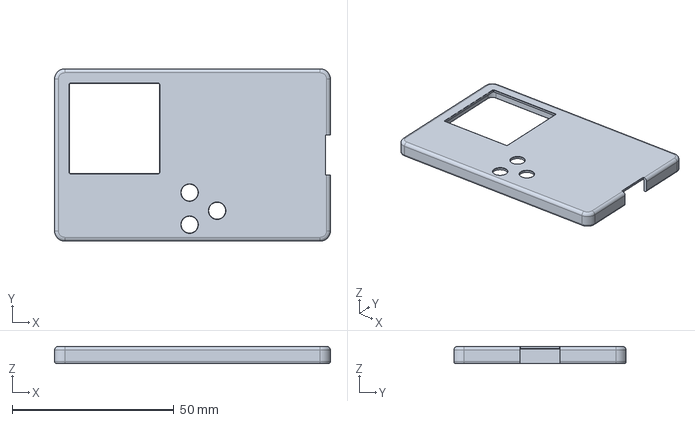
[picture p52: CAD file, 2026-09-24]
projects/nfc-business-card/enclosure/r1-usb-height-5.4/upper.step
85.2 x 53.2 x 5.40 mm
