Lin-Guanguo/hardware-lab/projects/nfc-business-card/enclosure/nfc-card-e16-bottom-v7.stl

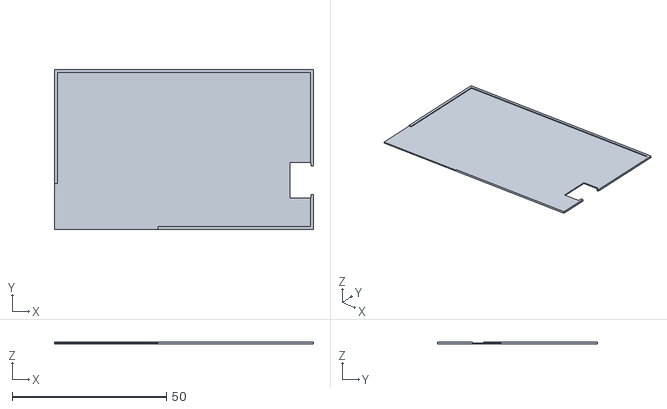
[picture p54: CAD file, 2026-09-22]
projects/nfc-business-card/enclosure/nfc-card-e16-bottom-v7.stl
84.0 x 52.0 x 0.7
