Lin-Guanguo/hardware-lab/projects/nfc-business-card/enclosure/pcba-e6-bottom-usb.FCStd

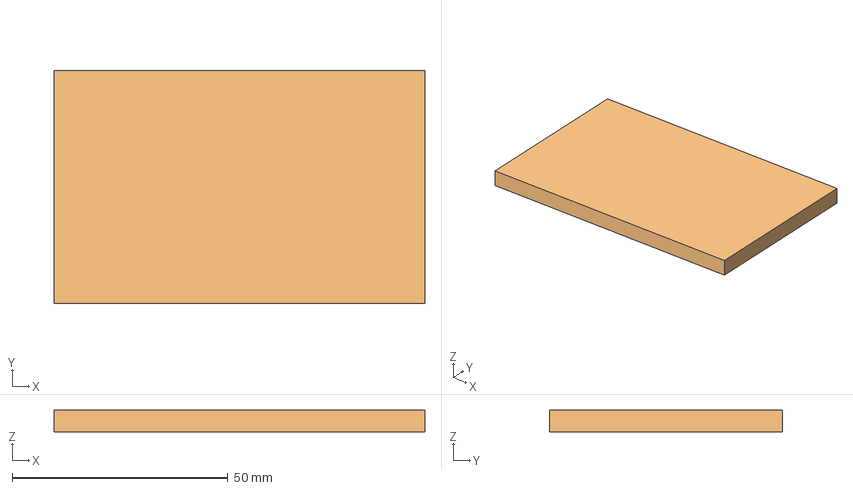
[picture p55: CAD file, 2026-09-22]
projects/nfc-business-card/enclosure/pcba-e6-bottom-usb.FCStd
86.0 x 54.0 x 5.00 mm
背壁预算面
86 × 54 × 5 mm
0.8 mm PCB · 电池缺口 / USB 槽假设
U1 · MDBT50Q-P1MV2
DS1 · GDEH0154E01 六色屏
BT1 · 302030 靠右横放
J1 · USB4500 下长边
USB 焊脚与装配区
J2 · 上接触 FPC 座待选
屏幕 FPC 路径与插入预留
六色屏升压器件区
NFC 专用区域
模块 2.4 GHz 天线预留
U2 · BQ25186
U3 · TPS7A0233
U4 · TPS22919 预留
电源与保护外围区
SWD 探针操作区
SW1 · SKQGABE010
按键 1 键帽与行程预留
SW2 · SKQGABE010
按键 2 键帽与行程预留
SW3 · SKQGABE010
按键 3 键帽与行程预留
电池出线/接点预留
CC 与 USB ESD 预留
