Lin-Guanguo/hardware-lab/projects/nfc-business-card/enclosure/nfc-card-e14-top-v1.stl

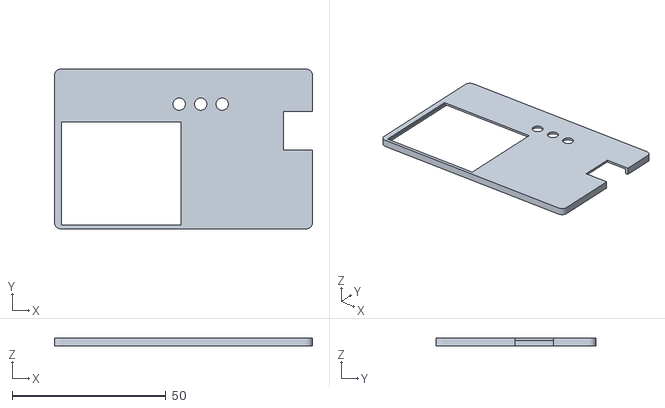
[picture p56: CAD file, 2026-09-22]
projects/nfc-business-card/enclosure/nfc-card-e14-top-v1.stl
84.0 x 52.0 x 2.60
