Lin-Guanguo/hardware-lab/projects/nfc-business-card/enclosure/pcba-e14-layout-envelope.step

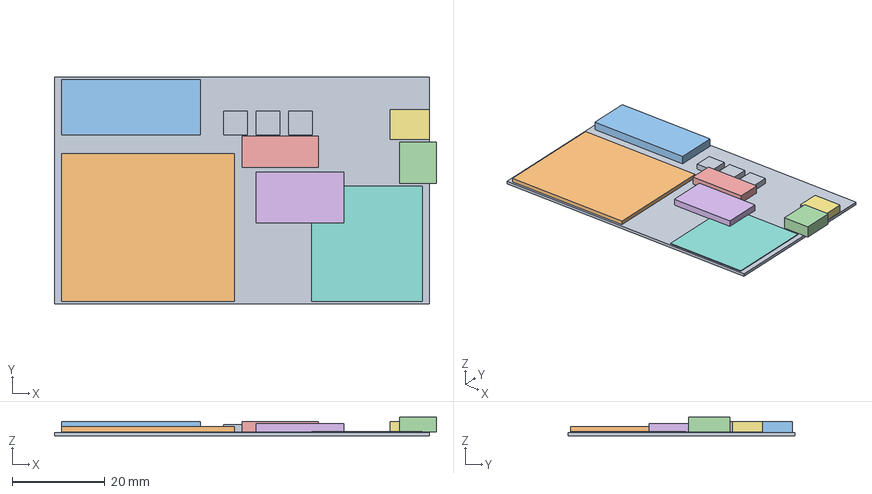
[picture p58: CAD file, 2026-09-22]
projects/nfc-business-card/enclosure/pcba-e14-layout-envelope.step
82.5 x 49.0 x 4.10 mm
