Lin-Guanguo/hardware-lab/projects/nfc-business-card/enclosure/pcba-layout.FCStd

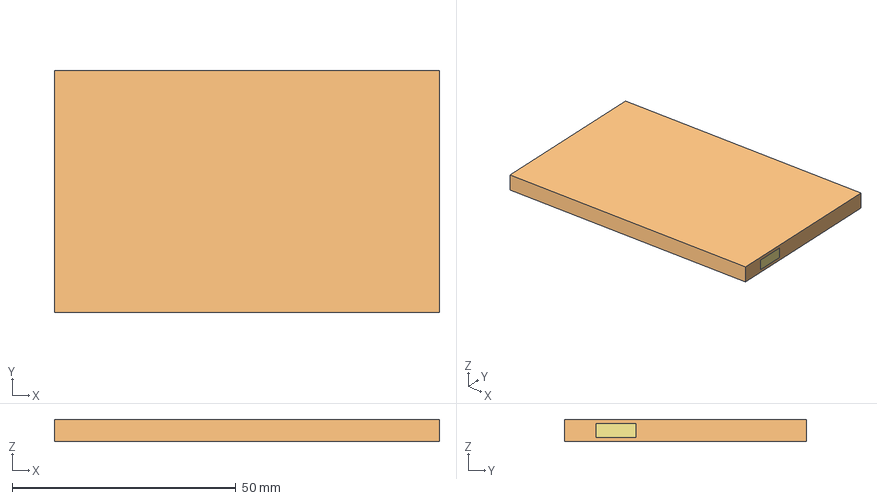
[picture p60: CAD file, 2026-09-22]
projects/nfc-business-card/enclosure/pcba-layout.FCStd
86.0 x 54.0 x 5.00 mm
背壁预算面
86 × 54 × 5 mm
0.8 mm PCB · 电池缺口 / USB 槽假设
U1 · MDBT50Q-P1MV2
DS1 · GDEY0154D67 玻璃
BT1 · 完整包体采购目标
J1 · USB4500 主体
USB 焊脚与装配区
J2 · FH12-24S
屏幕 FPC 路径与插入预留
屏幕升压器件区
NFC 专用区域
模块 2.4 GHz 天线预留
U2 · BQ25186
U3 · TPS7A0233
U4 · TPS22919 预留
电源与保护外围区
SWD 探针操作区
SW1 · SKQGABE010
按键 1 键帽与行程预留
SW2 · SKQGABE010
按键 2 键帽与行程预留
SW3 · SKQGABE010
按键 3 键帽与行程预留
