Lin-Guanguo/hardware-lab/projects/nfc-business-card/enclosure/nfc-card-e14-bottom-v1.stl

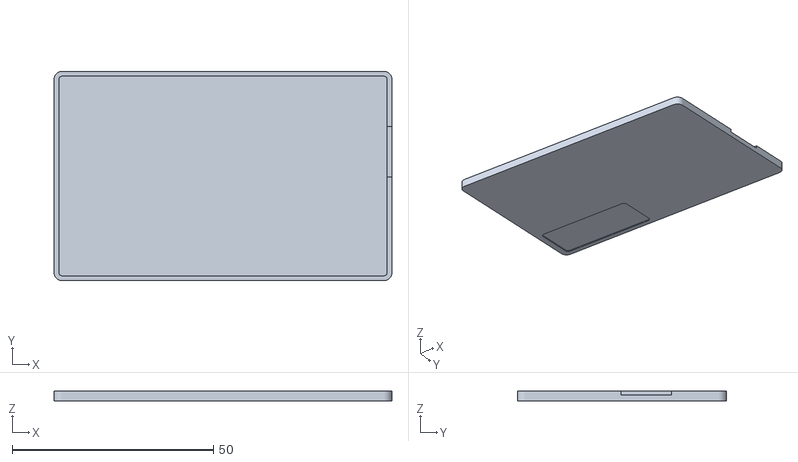
[picture p62: CAD file, 2026-09-22]
projects/nfc-business-card/enclosure/nfc-card-e14-bottom-v1.stl
84.0 x 52.0 x 2.40
