Lin-Guanguo/hardware-lab/projects/nfc-business-card/enclosure/nfc-card-e14-enclosure-v1.step

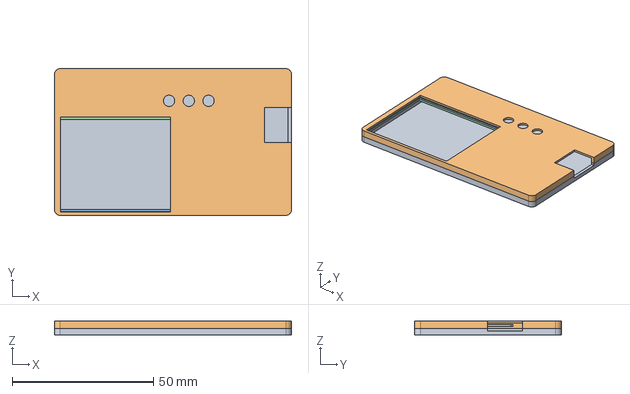
[picture p63: CAD file, 2026-09-22]
projects/nfc-business-card/enclosure/nfc-card-e14-enclosure-v1.step
84.0 x 52.0 x 5.00 mm
