Lin-Guanguo/hardware-lab/projects/nfc-business-card/enclosure/pcba-e14-battery-layout.FCStd

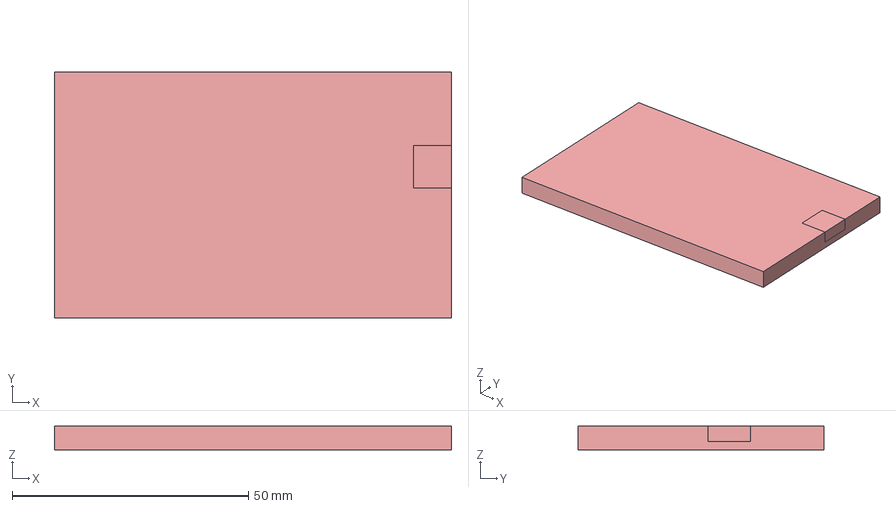
[picture p64: CAD file, 2026-09-22]
projects/nfc-business-card/enclosure/pcba-e14-battery-layout.FCStd
84.0 x 52.0 x 5.00 mm
PCB · 84 × 52 × 0.8 mm
屏幕 · GDEH0154E01 包络
电池 · 301230 标称 30 × 12 × 3 mm
NFC 右上净空
USB-C · J1 主体
J2 · FPC 座目标
USB/充电/稳压区
U1 · MDBT50Q 主控
SW1 · 按键包络
SW2 · 按键包络
SW3 · 按键包络
前盖窗口/按键/USB 待设计区
84 × 52 × 5 mm 目标包络
