Lin-Guanguo/hardware-lab/projects/nfc-business-card/enclosure/layout-study.FCStd

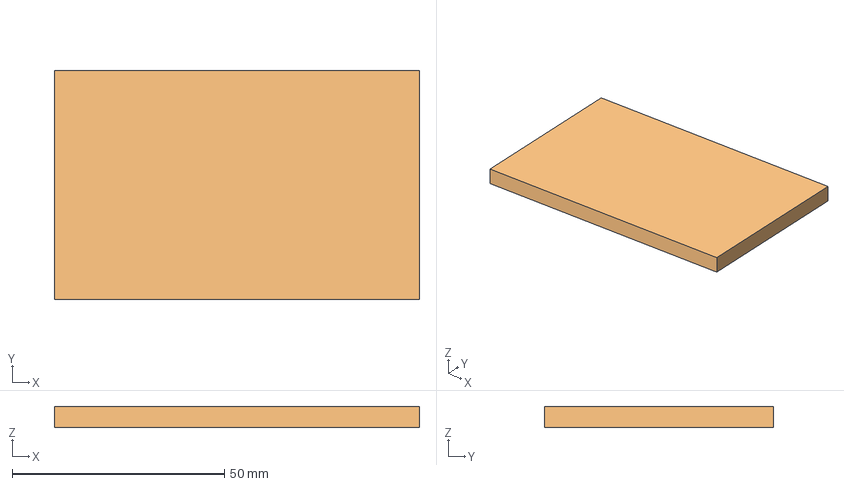
[picture p65: CAD file, 2026-09-20]
projects/nfc-business-card/enclosure/layout-study.FCStd
86.0 x 54.0 x 5.00 mm
背壁试算 0.8 mm
86 × 54 × 5 mm 外形目标
主控候选 · 商家标称 34.1 × 18 × 3.2
墨水屏玻璃 · 图纸尺寸上界
电池 · 目录标称（非完整包体上界）
NFC 空间分配 · 非天线设计
按键 1 · 仅主体
按键 2 · 仅主体
按键 3 · 仅主体
